tayspen72/BluetoothBlinker/BluetoothBlinker-MCU-rust/src/main.rs

//==============================================================================
// Notes
//==============================================================================
// main.rs

//==============================================================================
// Crates and Mods
//==============================================================================
#![no_std]
#![no_main]

use cortex_m_rt::entry;
use panic_halt as _; // Breakpoint on `rust_begin_unwind` to catch panics

mod config;
mod mcu;

//==============================================================================
// Enums, Structs, and Types
//==============================================================================


//==============================================================================
// Variables
//==============================================================================


//==============================================================================
// Main
//==============================================================================
#[entry]
fn main() -> ! {

	init();
	
	loop {
		task_handler();
	}
}

//==============================================================================
// Private Functions
//==============================================================================
fn init() {
	mcu::init();
}

//==============================================================================
// Task Handler
//==============================================================================
fn task_handler() {
	mcu::task_handler();
}
