tayspen72/BluetoothBlinker/BluetoothBlinker-MCU-c/cc26x0r2/inc/hw_ccfg.h

/******************************************************************************
*  Filename:       hw_ccfg_h
*  Revised:        2017-02-16 09:17:04 +0100 (Thu, 16 Feb 2017)
*  Revision:       48471
*
* Copyright (c) 2015 - 2017, Texas Instruments Incorporated
* All rights reserved.
*
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
* 3) Neither the name of the ORGANIZATION nor the names of its contributors may
*    be used to endorse or promote products derived from this software without
*    specific prior written permission.
*
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
******************************************************************************/

#ifndef __HW_CCFG_H__
#define __HW_CCFG_H__

//*****************************************************************************
//
// This section defines the register offsets of
// CCFG component
//
//*****************************************************************************
// Extern LF clock configuration
#define CCFG_O_EXT_LF_CLK                                           0x00000FA8

// Mode Configuration 1
#define CCFG_O_MODE_CONF_1                                          0x00000FAC

// CCFG Size and Disable Flags
#define CCFG_O_SIZE_AND_DIS_FLAGS                                   0x00000FB0

// Mode Configuration 0
#define CCFG_O_MODE_CONF                                            0x00000FB4

// Voltage Load 0
#define CCFG_O_VOLT_LOAD_0                                          0x00000FB8

// Voltage Load 1
#define CCFG_O_VOLT_LOAD_1                                          0x00000FBC

// Real Time Clock Offset
#define CCFG_O_RTC_OFFSET                                           0x00000FC0

// Frequency Offset
#define CCFG_O_FREQ_OFFSET                                          0x00000FC4

// IEEE MAC Address 0
#define CCFG_O_IEEE_MAC_0                                           0x00000FC8

// IEEE MAC Address 1
#define CCFG_O_IEEE_MAC_1                                           0x00000FCC

// IEEE BLE Address 0
#define CCFG_O_IEEE_BLE_0                                           0x00000FD0

// IEEE BLE Address 1
#define CCFG_O_IEEE_BLE_1                                           0x00000FD4

// Bootloader Configuration
#define CCFG_O_BL_CONFIG                                            0x00000FD8

// Erase Configuration
#define CCFG_O_ERASE_CONF                                           0x00000FDC

// TI Options
#define CCFG_O_CCFG_TI_OPTIONS                                      0x00000FE0

// Test Access Points Enable 0
#define CCFG_O_CCFG_TAP_DAP_0                                       0x00000FE4

// Test Access Points Enable 1
#define CCFG_O_CCFG_TAP_DAP_1                                       0x00000FE8

// Image Valid
#define CCFG_O_IMAGE_VALID_CONF                                     0x00000FEC

// Protect Sectors 0-31
#define CCFG_O_CCFG_PROT_31_0                                       0x00000FF0

// Protect Sectors 32-63
#define CCFG_O_CCFG_PROT_63_32                                      0x00000FF4

// Protect Sectors 64-95
#define CCFG_O_CCFG_PROT_95_64                                      0x00000FF8

// Protect Sectors 96-127
#define CCFG_O_CCFG_PROT_127_96                                     0x00000FFC

//*****************************************************************************
//
// Register: CCFG_O_EXT_LF_CLK
//
//*****************************************************************************
// Field: [31:24] DIO
//
// Unsigned integer, selecting the DIO to supply external 32kHz clock as
// SCLK_LF when MODE_CONF.SCLK_LF_OPTION is set to EXTERNAL. The selected DIO
// will be marked as reserved by the pin driver (TI-RTOS environment) and hence
// not selectable for other usage.
#define CCFG_EXT_LF_CLK_DIO_W                                                8
#define CCFG_EXT_LF_CLK_DIO_M                                       0xFF000000
#define CCFG_EXT_LF_CLK_DIO_S                                               24

// Field:  [23:0] RTC_INCREMENT
//
// Unsigned integer, defining the input frequency of the external clock and is
// written to AON_RTC:SUBSECINC.VALUEINC. Defined as follows:
// EXT_LF_CLK.RTC_INCREMENT = 2^38/InputClockFrequency in Hertz (e.g.:
// RTC_INCREMENT=0x800000 for InputClockFrequency=32768 Hz)
#define CCFG_EXT_LF_CLK_RTC_INCREMENT_W                                     24
#define CCFG_EXT_LF_CLK_RTC_INCREMENT_M                             0x00FFFFFF
#define CCFG_EXT_LF_CLK_RTC_INCREMENT_S                                      0

//*****************************************************************************
//
// Register: CCFG_O_MODE_CONF_1
//
//*****************************************************************************
// Field: [23:20] ALT_DCDC_VMIN
//
// Minimum voltage for when DC/DC should be used if alternate DC/DC setting is
// enabled (SIZE_AND_DIS_FLAGS.DIS_ALT_DCDC_SETTING=0).
// Voltage = (28 + ALT_DCDC_VMIN) / 16.
// 0: 1.75V
// 1: 1.8125V
// ...
// 14: 2.625V
// 15: 2.6875V
//
// NOTE! The DriverLib function SysCtrl_DCDC_VoltageConditionalControl() must
// be called regularly to apply this field (handled automatically if using TI
// RTOS!).
#define CCFG_MODE_CONF_1_ALT_DCDC_VMIN_W                                     4
#define CCFG_MODE_CONF_1_ALT_DCDC_VMIN_M                            0x00F00000
#define CCFG_MODE_CONF_1_ALT_DCDC_VMIN_S                                    20

// Field:    [19] ALT_DCDC_DITHER_EN
//
// Enable DC/DC dithering if alternate DC/DC setting is enabled
// (SIZE_AND_DIS_FLAGS.DIS_ALT_DCDC_SETTING=0).
// 0: Dither disable
// 1: Dither enable
#define CCFG_MODE_CONF_1_ALT_DCDC_DITHER_EN                         0x00080000
#define CCFG_MODE_CONF_1_ALT_DCDC_DITHER_EN_BITN                            19
#define CCFG_MODE_CONF_1_ALT_DCDC_DITHER_EN_M                       0x00080000
#define CCFG_MODE_CONF_1_ALT_DCDC_DITHER_EN_S                               19

// Field: [18:16] ALT_DCDC_IPEAK
//
// Inductor peak current if alternate DC/DC setting is enabled
// (SIZE_AND_DIS_FLAGS.DIS_ALT_DCDC_SETTING=0). Assuming 10uH external
// inductor!
// Peak current = 31 + ( 4 * ALT_DCDC_IPEAK ) :
// 0: 31mA (min)
// ...
// 4: 47mA
// ...
// 7: 59mA (max)
#define CCFG_MODE_CONF_1_ALT_DCDC_IPEAK_W                                    3
#define CCFG_MODE_CONF_1_ALT_DCDC_IPEAK_M                           0x00070000
#define CCFG_MODE_CONF_1_ALT_DCDC_IPEAK_S                                   16

// Field: [15:12] DELTA_IBIAS_INIT
//
// Signed delta value for IBIAS_INIT. Delta value only applies if
// SIZE_AND_DIS_FLAGS.DIS_XOSC_OVR=0.
// See FCFG1:AMPCOMP_CTRL1.IBIAS_INIT
#define CCFG_MODE_CONF_1_DELTA_IBIAS_INIT_W                                  4
#define CCFG_MODE_CONF_1_DELTA_IBIAS_INIT_M                         0x0000F000
#define CCFG_MODE_CONF_1_DELTA_IBIAS_INIT_S                                 12

// Field:  [11:8] DELTA_IBIAS_OFFSET
//
// Signed delta value for IBIAS_OFFSET. Delta value only applies if
// SIZE_AND_DIS_FLAGS.DIS_XOSC_OVR=0.
// See FCFG1:AMPCOMP_CTRL1.IBIAS_OFFSET
#define CCFG_MODE_CONF_1_DELTA_IBIAS_OFFSET_W                                4
#define CCFG_MODE_CONF_1_DELTA_IBIAS_OFFSET_M                       0x00000F00
#define CCFG_MODE_CONF_1_DELTA_IBIAS_OFFSET_S                                8

// Field:   [7:0] XOSC_MAX_START
//
// Unsigned value of maximum XOSC startup time (worst case) in units of 100us.
// Value only applies if SIZE_AND_DIS_FLAGS.DIS_XOSC_OVR=0.
#define CCFG_MODE_CONF_1_XOSC_MAX_START_W                                    8
#define CCFG_MODE_CONF_1_XOSC_MAX_START_M                           0x000000FF
#define CCFG_MODE_CONF_1_XOSC_MAX_START_S                                    0

//*****************************************************************************
//
// Register: CCFG_O_SIZE_AND_DIS_FLAGS
//
//*****************************************************************************
// Field: [31:16] SIZE_OF_CCFG
//
// Total size of CCFG in bytes.
#define CCFG_SIZE_AND_DIS_FLAGS_SIZE_OF_CCFG_W                              16
#define CCFG_SIZE_AND_DIS_FLAGS_SIZE_OF_CCFG_M                      0xFFFF0000
#define CCFG_SIZE_AND_DIS_FLAGS_SIZE_OF_CCFG_S                              16

// Field:  [15:4] DISABLE_FLAGS
//
// Reserved for future use. Software should not rely on the value of a
// reserved. Writing any other value than the reset/default value may result in
// undefined behavior.
#define CCFG_SIZE_AND_DIS_FLAGS_DISABLE_FLAGS_W                             12
#define CCFG_SIZE_AND_DIS_FLAGS_DISABLE_FLAGS_M                     0x0000FFF0
#define CCFG_SIZE_AND_DIS_FLAGS_DISABLE_FLAGS_S                              4

// Field:     [3] DIS_TCXO
//
// Disable TCXO.
// 0: TCXO functionality enabled.
// 1: TCXO functionality disabled.
// Note:
// An external TCXO is required if DIS_TCXO = 0.
#define CCFG_SIZE_AND_DIS_FLAGS_DIS_TCXO                            0x00000008
#define CCFG_SIZE_AND_DIS_FLAGS_DIS_TCXO_BITN                                3
#define CCFG_SIZE_AND_DIS_FLAGS_DIS_TCXO_M                          0x00000008
#define CCFG_SIZE_AND_DIS_FLAGS_DIS_TCXO_S                                   3

// Field:     [2] DIS_GPRAM
//
// Disable GPRAM (or use the 8K VIMS RAM as CACHE RAM).
// 0: GPRAM is enabled and hence CACHE disabled.
// 1: GPRAM is disabled and instead CACHE is enabled (default).
// Notes:
// - Disabling CACHE will reduce CPU execution speed (up to 60%).
// - GPRAM is 8 K-bytes in size and located at 0x11000000-0x11001FFF if
// enabled.
// See:
// VIMS:CTL.MODE
#define CCFG_SIZE_AND_DIS_FLAGS_DIS_GPRAM                           0x00000004
#define CCFG_SIZE_AND_DIS_FLAGS_DIS_GPRAM_BITN                               2
#define CCFG_SIZE_AND_DIS_FLAGS_DIS_GPRAM_M                         0x00000004
#define CCFG_SIZE_AND_DIS_FLAGS_DIS_GPRAM_S                                  2

// Field:     [1] DIS_ALT_DCDC_SETTING
//
// Disable alternate DC/DC settings.
// 0: Enable alternate DC/DC settings.
// 1: Disable alternate DC/DC settings.
// See:
// MODE_CONF_1.ALT_DCDC_VMIN
// MODE_CONF_1.ALT_DCDC_DITHER_EN
// MODE_CONF_1.ALT_DCDC_IPEAK
//
// NOTE! The DriverLib function SysCtrl_DCDC_VoltageConditionalControl() must
// be called regularly to apply this field (handled automatically if using TI
// RTOS!).
#define CCFG_SIZE_AND_DIS_FLAGS_DIS_ALT_DCDC_SETTING                0x00000002
#define CCFG_SIZE_AND_DIS_FLAGS_DIS_ALT_DCDC_SETTING_BITN                    1
#define CCFG_SIZE_AND_DIS_FLAGS_DIS_ALT_DCDC_SETTING_M              0x00000002
#define CCFG_SIZE_AND_DIS_FLAGS_DIS_ALT_DCDC_SETTING_S                       1

// Field:     [0] DIS_XOSC_OVR
//
// Disable XOSC override functionality.
// 0: Enable XOSC override functionality.
// 1: Disable XOSC override functionality.
// See:
// MODE_CONF_1.DELTA_IBIAS_INIT
// MODE_CONF_1.DELTA_IBIAS_OFFSET
// MODE_CONF_1.XOSC_MAX_START
#define CCFG_SIZE_AND_DIS_FLAGS_DIS_XOSC_OVR                        0x00000001
#define CCFG_SIZE_AND_DIS_FLAGS_DIS_XOSC_OVR_BITN                            0
#define CCFG_SIZE_AND_DIS_FLAGS_DIS_XOSC_OVR_M                      0x00000001
#define CCFG_SIZE_AND_DIS_FLAGS_DIS_XOSC_OVR_S                               0

//*****************************************************************************
//
// Register: CCFG_O_MODE_CONF
//
//*****************************************************************************
// Field: [31:28] VDDR_TRIM_SLEEP_DELTA
//
// Signed delta value to apply to the
// VDDR_TRIM_SLEEP target, minus one. See FCFG1:VOLT_TRIM.VDDR_TRIM_SLEEP_H.
// 0x8 (-8) : Delta = -7
// ...
// 0xF (-1) : Delta = 0
// 0x0 (0) : Delta = +1
// ...
// 0x7 (7) : Delta = +8
#define CCFG_MODE_CONF_VDDR_TRIM_SLEEP_DELTA_W                               4
#define CCFG_MODE_CONF_VDDR_TRIM_SLEEP_DELTA_M                      0xF0000000
#define CCFG_MODE_CONF_VDDR_TRIM_SLEEP_DELTA_S                              28

// Field:    [27] DCDC_RECHARGE
//
// DC/DC during recharge in powerdown.
// 0: Use the DC/DC during recharge in powerdown.
// 1: Do not use the DC/DC during recharge in powerdown (default).
//
// NOTE! The DriverLib function SysCtrl_DCDC_VoltageConditionalControl() must
// be called regularly to apply this field (handled automatically if using TI
// RTOS!).
#define CCFG_MODE_CONF_DCDC_RECHARGE                                0x08000000
#define CCFG_MODE_CONF_DCDC_RECHARGE_BITN                                   27
#define CCFG_MODE_CONF_DCDC_RECHARGE_M                              0x08000000
#define CCFG_MODE_CONF_DCDC_RECHARGE_S                                      27

// Field:    [26] DCDC_ACTIVE
//
// DC/DC in active mode.
// 0: Use the DC/DC during active mode.
// 1: Do not use the DC/DC during active mode (default).
//
// NOTE! The DriverLib function SysCtrl_DCDC_VoltageConditionalControl() must
// be called regularly to apply this field (handled automatically if using TI
// RTOS!).
#define CCFG_MODE_CONF_DCDC_ACTIVE                                  0x04000000
#define CCFG_MODE_CONF_DCDC_ACTIVE_BITN                                     26
#define CCFG_MODE_CONF_DCDC_ACTIVE_M                                0x04000000
#define CCFG_MODE_CONF_DCDC_ACTIVE_S                                        26

// Field:    [25] VDDR_EXT_LOAD
//
// Reserved for future use. Software should not rely on the value of a
// reserved. Writing any other value than the reset/default value may result in
// undefined behavior.
#define CCFG_MODE_CONF_VDDR_EXT_LOAD                                0x02000000
#define CCFG_MODE_CONF_VDDR_EXT_LOAD_BITN                                   25
#define CCFG_MODE_CONF_VDDR_EXT_LOAD_M                              0x02000000
#define CCFG_MODE_CONF_VDDR_EXT_LOAD_S                                      25

// Field:    [24] VDDS_BOD_LEVEL
//
// VDDS BOD level.
// 0: VDDS BOD level is 2.0 V (necessary for maximum PA output power on
// CC13x0).
// 1: VDDS BOD level is 1.8 V (or 1.7 V for external regulator mode) (default).
#define CCFG_MODE_CONF_VDDS_BOD_LEVEL                               0x01000000
#define CCFG_MODE_CONF_VDDS_BOD_LEVEL_BITN                                  24
#define CCFG_MODE_CONF_VDDS_BOD_LEVEL_M                             0x01000000
#define CCFG_MODE_CONF_VDDS_BOD_LEVEL_S                                     24

// Field: [23:22] SCLK_LF_OPTION
//
// Select source for SCLK_LF.
// ENUMs:
// RCOSC_LF                 Low frequency RCOSC (default)
// XOSC_LF                  32.768kHz low frequency XOSC
// EXTERNAL_LF              External low frequency clock on DIO defined by
//                          EXT_LF_CLK.DIO. The RTC tick speed
//                          AON_RTC:SUBSECINC is updated to
//                          EXT_LF_CLK.RTC_INCREMENT (done in the
//                          trimDevice() xxWare boot function). External
//                          clock must always be running when the chip is
//                          in standby for VDDR recharge timing.
// XOSC_HF_DLF              31.25kHz clock derived from 24MHz XOSC (dividing
//                          by 768 in HW). The RTC tick speed
//                          [AON_RTC.SUBSECINC.*] is updated to 0x8637BD,
//                          corresponding to a 31.25kHz clock (done in the
//                          trimDevice() xxWare boot function). Standby
//                          power mode is not supported when using this
//                          clock source.
#define CCFG_MODE_CONF_SCLK_LF_OPTION_W                                      2
#define CCFG_MODE_CONF_SCLK_LF_OPTION_M                             0x00C00000
#define CCFG_MODE_CONF_SCLK_LF_OPTION_S                                     22
#define CCFG_MODE_CONF_SCLK_LF_OPTION_RCOSC_LF                      0x00C00000
#define CCFG_MODE_CONF_SCLK_LF_OPTION_XOSC_LF                       0x00800000
#define CCFG_MODE_CONF_SCLK_LF_OPTION_EXTERNAL_LF                   0x00400000
#define CCFG_MODE_CONF_SCLK_LF_OPTION_XOSC_HF_DLF                   0x00000000

// Field:    [21] VDDR_TRIM_SLEEP_TC
//
// 0x1: VDDR_TRIM_SLEEP_DELTA is not temperature compensated
// 0x0: RTOS/driver temperature compensates VDDR_TRIM_SLEEP_DELTA every time
// standby mode is entered. This improves low-temperature RCOSC_LF frequency
// stability in standby mode.
//
// When temperature compensation is performed, the delta is calculates this
// way:
// Delta = max (delta, min(8, floor(62-temp)/8))
// Here, delta is given by VDDR_TRIM_SLEEP_DELTA, and temp is the current
// temperature in degrees C.
#define CCFG_MODE_CONF_VDDR_TRIM_SLEEP_TC                           0x00200000
#define CCFG_MODE_CONF_VDDR_TRIM_SLEEP_TC_BITN                              21
#define CCFG_MODE_CONF_VDDR_TRIM_SLEEP_TC_M                         0x00200000
#define CCFG_MODE_CONF_VDDR_TRIM_SLEEP_TC_S                                 21

// Field:    [20] RTC_COMP
//
// Reserved for future use. Software should not rely on the value of a
// reserved. Writing any other value than the reset/default value may result in
// undefined behavior.
#define CCFG_MODE_CONF_RTC_COMP                                     0x00100000
#define CCFG_MODE_CONF_RTC_COMP_BITN                                        20
#define CCFG_MODE_CONF_RTC_COMP_M                                   0x00100000
#define CCFG_MODE_CONF_RTC_COMP_S                                           20

// Field: [19:18] XOSC_FREQ
//
// Reserved for future use. Software should not rely on the value of a
// reserved. Writing any other value than the reset/default value may result in
// undefined behavior.
// ENUMs:
// 24M                      24 MHz XOSC_HF
// 48M                      48 MHz XOSC_HF
// HPOSC                    HPOSC
#define CCFG_MODE_CONF_XOSC_FREQ_W                                           2
#define CCFG_MODE_CONF_XOSC_FREQ_M                                  0x000C0000
#define CCFG_MODE_CONF_XOSC_FREQ_S                                          18
#define CCFG_MODE_CONF_XOSC_FREQ_24M                                0x000C0000
#define CCFG_MODE_CONF_XOSC_FREQ_48M                                0x00080000
#define CCFG_MODE_CONF_XOSC_FREQ_HPOSC                              0x00040000

// Field:    [17] XOSC_CAP_MOD
//
// Enable modification (delta) to XOSC cap-array. Value specified in
// XOSC_CAPARRAY_DELTA.
// 0: Apply cap-array delta
// 1: Do not apply cap-array delta (default)
#define CCFG_MODE_CONF_XOSC_CAP_MOD                                 0x00020000
#define CCFG_MODE_CONF_XOSC_CAP_MOD_BITN                                    17
#define CCFG_MODE_CONF_XOSC_CAP_MOD_M                               0x00020000
#define CCFG_MODE_CONF_XOSC_CAP_MOD_S                                       17

// Field:    [16] HF_COMP
//
// Reserved for future use. Software should not rely on the value of a
// reserved. Writing any other value than the reset/default value may result in
// undefined behavior.
#define CCFG_MODE_CONF_HF_COMP                                      0x00010000
#define CCFG_MODE_CONF_HF_COMP_BITN                                         16
#define CCFG_MODE_CONF_HF_COMP_M                                    0x00010000
#define CCFG_MODE_CONF_HF_COMP_S                                            16

// Field:  [15:8] XOSC_CAPARRAY_DELTA
//
// Signed 8-bit value, directly modifying trimmed XOSC cap-array step value.
// Enabled by XOSC_CAP_MOD.
#define CCFG_MODE_CONF_XOSC_CAPARRAY_DELTA_W                                 8
#define CCFG_MODE_CONF_XOSC_CAPARRAY_DELTA_M                        0x0000FF00
#define CCFG_MODE_CONF_XOSC_CAPARRAY_DELTA_S                                 8

// Field:   [7:0] VDDR_CAP
//
// Unsigned 8-bit integer, representing the minimum decoupling capacitance
// (worst case) on VDDR, in units of 100nF. This should take into account
// capacitor tolerance and voltage dependent capacitance variation. This bit
// affects the recharge period calculation when going into powerdown or
// standby.
//
// NOTE! If using the following functions this field must be configured (used
// by TI RTOS):
// SysCtrlSetRechargeBeforePowerDown() SysCtrlAdjustRechargeAfterPowerDown()
#define CCFG_MODE_CONF_VDDR_CAP_W                                            8
#define CCFG_MODE_CONF_VDDR_CAP_M                                   0x000000FF
#define CCFG_MODE_CONF_VDDR_CAP_S                                            0

//*****************************************************************************
//
// Register: CCFG_O_VOLT_LOAD_0
//
//*****************************************************************************
// Field: [31:24] VDDR_EXT_TP45
//
// Reserved for future use. Software should not rely on the value of a
// reserved. Writing any other value than the reset/default value may result in
// undefined behavior.
#define CCFG_VOLT_LOAD_0_VDDR_EXT_TP45_W                                     8
#define CCFG_VOLT_LOAD_0_VDDR_EXT_TP45_M                            0xFF000000
#define CCFG_VOLT_LOAD_0_VDDR_EXT_TP45_S                                    24

// Field: [23:16] VDDR_EXT_TP25
//
// Reserved for future use. Software should not rely on the value of a
// reserved. Writing any other value than the reset/default value may result in
// undefined behavior.
#define CCFG_VOLT_LOAD_0_VDDR_EXT_TP25_W                                     8
#define CCFG_VOLT_LOAD_0_VDDR_EXT_TP25_M                            0x00FF0000
#define CCFG_VOLT_LOAD_0_VDDR_EXT_TP25_S                                    16

// Field:  [15:8] VDDR_EXT_TP5
//
// Reserved for future use. Software should not rely on the value of a
// reserved. Writing any other value than the reset/default value may result in
// undefined behavior.
#define CCFG_VOLT_LOAD_0_VDDR_EXT_TP5_W                                      8
#define CCFG_VOLT_LOAD_0_VDDR_EXT_TP5_M                             0x0000FF00
#define CCFG_VOLT_LOAD_0_VDDR_EXT_TP5_S                                      8

// Field:   [7:0] VDDR_EXT_TM15
//
// Reserved for future use. Software should not rely on the value of a
// reserved. Writing any other value than the reset/default value may result in
// undefined behavior.
#define CCFG_VOLT_LOAD_0_VDDR_EXT_TM15_W                                     8
#define CCFG_VOLT_LOAD_0_VDDR_EXT_TM15_M                            0x000000FF
#define CCFG_VOLT_LOAD_0_VDDR_EXT_TM15_S                                     0

//*****************************************************************************
//
// Register: CCFG_O_VOLT_LOAD_1
//
//*****************************************************************************
// Field: [31:24] VDDR_EXT_TP125
//
// Reserved for future use. Software should not rely on the value of a
// reserved. Writing any other value than the reset/default value may result in
// undefined behavior.
#define CCFG_VOLT_LOAD_1_VDDR_EXT_TP125_W                                    8
#define CCFG_VOLT_LOAD_1_VDDR_EXT_TP125_M                           0xFF000000
#define CCFG_VOLT_LOAD_1_VDDR_EXT_TP125_S                                   24

// Field: [23:16] VDDR_EXT_TP105
//
// Reserved for future use. Software should not rely on the value of a
// reserved. Writing any other value than the reset/default value may result in
// undefined behavior.
#define CCFG_VOLT_LOAD_1_VDDR_EXT_TP105_W                                    8
#define CCFG_VOLT_LOAD_1_VDDR_EXT_TP105_M                           0x00FF0000
#define CCFG_VOLT_LOAD_1_VDDR_EXT_TP105_S                                   16

// Field:  [15:8] VDDR_EXT_TP85
//
// Reserved for future use. Software should not rely on the value of a
// reserved. Writing any other value than the reset/default value may result in
// undefined behavior.
#define CCFG_VOLT_LOAD_1_VDDR_EXT_TP85_W                                     8
#define CCFG_VOLT_LOAD_1_VDDR_EXT_TP85_M                            0x0000FF00
#define CCFG_VOLT_LOAD_1_VDDR_EXT_TP85_S                                     8

// Field:   [7:0] VDDR_EXT_TP65
//
// Reserved for future use. Software should not rely on the value of a
// reserved. Writing any other value than the reset/default value may result in
// undefined behavior.
#define CCFG_VOLT_LOAD_1_VDDR_EXT_TP65_W                                     8
#define CCFG_VOLT_LOAD_1_VDDR_EXT_TP65_M                            0x000000FF
#define CCFG_VOLT_LOAD_1_VDDR_EXT_TP65_S                                     0

//*****************************************************************************
//
// Register: CCFG_O_RTC_OFFSET
//
//*****************************************************************************
// Field: [31:16] RTC_COMP_P0
//
// Reserved for future use. Software should not rely on the value of a
// reserved. Writing any other value than the reset/default value may result in
// undefined behavior.
#define CCFG_RTC_OFFSET_RTC_COMP_P0_W                                       16
#define CCFG_RTC_OFFSET_RTC_COMP_P0_M                               0xFFFF0000
#define CCFG_RTC_OFFSET_RTC_COMP_P0_S                                       16

// Field:  [15:8] RTC_COMP_P1
//
// Reserved for future use. Software should not rely on the value of a
// reserved. Writing any other value than the reset/default value may result in
// undefined behavior.
#define CCFG_RTC_OFFSET_RTC_COMP_P1_W                                        8
#define CCFG_RTC_OFFSET_RTC_COMP_P1_M                               0x0000FF00
#define CCFG_RTC_OFFSET_RTC_COMP_P1_S                                        8

// Field:   [7:0] RTC_COMP_P2
//
// Reserved for future use. Software should not rely on the value of a
// reserved. Writing any other value than the reset/default value may result in
// undefined behavior.
#define CCFG_RTC_OFFSET_RTC_COMP_P2_W                                        8
#define CCFG_RTC_OFFSET_RTC_COMP_P2_M                               0x000000FF
#define CCFG_RTC_OFFSET_RTC_COMP_P2_S                                        0

//*****************************************************************************
//
// Register: CCFG_O_FREQ_OFFSET
//
//*****************************************************************************
// Field: [31:16] HF_COMP_P0
//
// Reserved for future use. Software should not rely on the value of a
// reserved. Writing any other value than the reset/default value may result in
// undefined behavior.
#define CCFG_FREQ_OFFSET_HF_COMP_P0_W                                       16
#define CCFG_FREQ_OFFSET_HF_COMP_P0_M                               0xFFFF0000
#define CCFG_FREQ_OFFSET_HF_COMP_P0_S                                       16

// Field:  [15:8] HF_COMP_P1
//
// Reserved for future use. Software should not rely on the value of a
// reserved. Writing any other value than the reset/default value may result in
// undefined behavior.
#define CCFG_FREQ_OFFSET_HF_COMP_P1_W                                        8
#define CCFG_FREQ_OFFSET_HF_COMP_P1_M                               0x0000FF00
#define CCFG_FREQ_OFFSET_HF_COMP_P1_S                                        8

// Field:   [7:0] HF_COMP_P2
//
// Reserved for future use. Software should not rely on the value of a
// reserved. Writing any other value than the reset/default value may result in
// undefined behavior.
#define CCFG_FREQ_OFFSET_HF_COMP_P2_W                                        8
#define CCFG_FREQ_OFFSET_HF_COMP_P2_M                               0x000000FF
#define CCFG_FREQ_OFFSET_HF_COMP_P2_S                                        0

//*****************************************************************************
//
// Register: CCFG_O_IEEE_MAC_0
//
//*****************************************************************************
// Field:  [31:0] ADDR
//
// Bits[31:0] of the 64-bits custom IEEE MAC address.
// If different from 0xFFFFFFFF then the value of this field is applied;
// otherwise use value from FCFG.
#define CCFG_IEEE_MAC_0_ADDR_W                                              32
#define CCFG_IEEE_MAC_0_ADDR_M                                      0xFFFFFFFF
#define CCFG_IEEE_MAC_0_ADDR_S                                               0

//*****************************************************************************
//
// Register: CCFG_O_IEEE_MAC_1
//
//*****************************************************************************
// Field:  [31:0] ADDR
//
// Bits[63:32] of the 64-bits custom IEEE MAC address.
// If different from 0xFFFFFFFF then the value of this field is applied;
// otherwise use value from FCFG.
#define CCFG_IEEE_MAC_1_ADDR_W                                              32
#define CCFG_IEEE_MAC_1_ADDR_M                                      0xFFFFFFFF
#define CCFG_IEEE_MAC_1_ADDR_S                                               0

//*****************************************************************************
//
// Register: CCFG_O_IEEE_BLE_0
//
//*****************************************************************************
// Field:  [31:0] ADDR
//
// Bits[31:0] of the 64-bits custom IEEE BLE address.
// If different from 0xFFFFFFFF then the value of this field is applied;
// otherwise use value from FCFG.
#define CCFG_IEEE_BLE_0_ADDR_W                                              32
#define CCFG_IEEE_BLE_0_ADDR_M                                      0xFFFFFFFF
#define CCFG_IEEE_BLE_0_ADDR_S                                               0

//*****************************************************************************
//
// Register: CCFG_O_IEEE_BLE_1
//
//*****************************************************************************
// Field:  [31:0] ADDR
//
// Bits[63:32] of the 64-bits custom IEEE BLE address.
// If different from 0xFFFFFFFF then the value of this field is applied;
// otherwise use value from FCFG.
#define CCFG_IEEE_BLE_1_ADDR_W                                              32
#define CCFG_IEEE_BLE_1_ADDR_M                                      0xFFFFFFFF
#define CCFG_IEEE_BLE_1_ADDR_S                                               0

//*****************************************************************************
//
// Register: CCFG_O_BL_CONFIG
//
//*****************************************************************************
// Field: [31:24] BOOTLOADER_ENABLE
//
// Bootloader enable. Boot loader can be accessed if
// IMAGE_VALID_CONF.IMAGE_VALID is non-zero or BL_ENABLE is enabled (and
// conditions for boot loader backdoor are met).
// 0xC5: Boot loader is enabled.
// Any other value: Boot loader is disabled.
#define CCFG_BL_CONFIG_BOOTLOADER_ENABLE_W                                   8
#define CCFG_BL_CONFIG_BOOTLOADER_ENABLE_M                          0xFF000000
#define CCFG_BL_CONFIG_BOOTLOADER_ENABLE_S                                  24

// Field:    [16] BL_LEVEL
//
// Sets the active level of the selected DIO number BL_PIN_NUMBER if boot
// loader backdoor is enabled by the BL_ENABLE field.
// 0: Active low.
// 1: Active high.
#define CCFG_BL_CONFIG_BL_LEVEL                                     0x00010000
#define CCFG_BL_CONFIG_BL_LEVEL_BITN                                        16
#define CCFG_BL_CONFIG_BL_LEVEL_M                                   0x00010000
#define CCFG_BL_CONFIG_BL_LEVEL_S                                           16

// Field:  [15:8] BL_PIN_NUMBER
//
// DIO number that is level checked if the boot loader backdoor is enabled by
// the BL_ENABLE field.
#define CCFG_BL_CONFIG_BL_PIN_NUMBER_W                                       8
#define CCFG_BL_CONFIG_BL_PIN_NUMBER_M                              0x0000FF00
#define CCFG_BL_CONFIG_BL_PIN_NUMBER_S                                       8

// Field:   [7:0] BL_ENABLE
//
// Enables the boot loader backdoor.
// 0xC5: Boot loader backdoor is enabled.
// Any other value: Boot loader backdoor is disabled.
//
// NOTE! Boot loader must be enabled (see BOOTLOADER_ENABLE) if boot loader
// backdoor is enabled.
#define CCFG_BL_CONFIG_BL_ENABLE_W                                           8
#define CCFG_BL_CONFIG_BL_ENABLE_M                                  0x000000FF
#define CCFG_BL_CONFIG_BL_ENABLE_S                                           0

//*****************************************************************************
//
// Register: CCFG_O_ERASE_CONF
//
//*****************************************************************************
// Field:     [8] CHIP_ERASE_DIS_N
//
// Chip erase.
// This bit controls if a chip erase requested through the JTAG WUC TAP will be
// ignored in a following boot caused by a reset of the MCU VD.
// A successful chip erase operation will force the content of the flash main
// bank back to the state as it was when delivered by TI.
// 0: Disable. Any chip erase request detected during boot will be ignored.
// 1: Enable. Any chip erase request detected during boot will be performed by
// the boot FW.
#define CCFG_ERASE_CONF_CHIP_ERASE_DIS_N                            0x00000100
#define CCFG_ERASE_CONF_CHIP_ERASE_DIS_N_BITN                                8
#define CCFG_ERASE_CONF_CHIP_ERASE_DIS_N_M                          0x00000100
#define CCFG_ERASE_CONF_CHIP_ERASE_DIS_N_S                                   8

// Field:     [0] BANK_ERASE_DIS_N
//
// Bank erase.
// This bit controls if the ROM serial boot loader will accept a received Bank
// Erase command (COMMAND_BANK_ERASE).
// A successful Bank Erase operation will erase all main bank sectors not
// protected by write protect configuration bits in CCFG.
// 0: Disable the boot loader bank erase function.
// 1: Enable the boot loader bank erase function.
#define CCFG_ERASE_CONF_BANK_ERASE_DIS_N                            0x00000001
#define CCFG_ERASE_CONF_BANK_ERASE_DIS_N_BITN                                0
#define CCFG_ERASE_CONF_BANK_ERASE_DIS_N_M                          0x00000001
#define CCFG_ERASE_CONF_BANK_ERASE_DIS_N_S                                   0

//*****************************************************************************
//
// Register: CCFG_O_CCFG_TI_OPTIONS
//
//*****************************************************************************
// Field:   [7:0] TI_FA_ENABLE
//
// TI Failure Analysis.
// 0xC5: Enable the functionality of unlocking the TI FA (TI Failure Analysis)
// option with the unlock code.
// All other values: Disable the functionality of unlocking the TI FA option
// with the unlock code.
#define CCFG_CCFG_TI_OPTIONS_TI_FA_ENABLE_W                                  8
#define CCFG_CCFG_TI_OPTIONS_TI_FA_ENABLE_M                         0x000000FF
#define CCFG_CCFG_TI_OPTIONS_TI_FA_ENABLE_S                                  0

//*****************************************************************************
//
// Register: CCFG_O_CCFG_TAP_DAP_0
//
//*****************************************************************************
// Field: [23:16] CPU_DAP_ENABLE
//
// Enable CPU DAP.
// 0xC5: Main CPU DAP access is enabled during power-up/system-reset by ROM
// boot FW.
// Any other value: Main CPU DAP access will remain disabled out of
// power-up/system-reset.
#define CCFG_CCFG_TAP_DAP_0_CPU_DAP_ENABLE_W                                 8
#define CCFG_CCFG_TAP_DAP_0_CPU_DAP_ENABLE_M                        0x00FF0000
#define CCFG_CCFG_TAP_DAP_0_CPU_DAP_ENABLE_S                                16

// Field:  [15:8] PRCM_TAP_ENABLE
//
// Enable PRCM TAP.
// 0xC5: PRCM TAP access is enabled during power-up/system-reset by ROM boot FW
// if enabled by corresponding configuration value in FCFG1 defined by TI.
// Any other value: PRCM TAP access will remain disabled out of
// power-up/system-reset.
#define CCFG_CCFG_TAP_DAP_0_PRCM_TAP_ENABLE_W                                8
#define CCFG_CCFG_TAP_DAP_0_PRCM_TAP_ENABLE_M                       0x0000FF00
#define CCFG_CCFG_TAP_DAP_0_PRCM_TAP_ENABLE_S                                8

// Field:   [7:0] TEST_TAP_ENABLE
//
// Enable Test TAP.
// 0xC5: TEST TAP access is enabled during power-up/system-reset by ROM boot FW
// if enabled by corresponding configuration value in FCFG1 defined by TI.
// Any other value: TEST TAP access will remain disabled out of
// power-up/system-reset.
#define CCFG_CCFG_TAP_DAP_0_TEST_TAP_ENABLE_W                                8
#define CCFG_CCFG_TAP_DAP_0_TEST_TAP_ENABLE_M                       0x000000FF
#define CCFG_CCFG_TAP_DAP_0_TEST_TAP_ENABLE_S                                0

//*****************************************************************************
//
// Register: CCFG_O_CCFG_TAP_DAP_1
//
//*****************************************************************************
// Field: [23:16] PBIST2_TAP_ENABLE
//
// Enable PBIST2 TAP.
// 0xC5: PBIST2 TAP access is enabled during power-up/system-reset by ROM boot
// FW if enabled by corresponding configuration value in FCFG1 defined by TI.
// Any other value: PBIST2 TAP access will remain disabled out of
// power-up/system-reset.
#define CCFG_CCFG_TAP_DAP_1_PBIST2_TAP_ENABLE_W                              8
#define CCFG_CCFG_TAP_DAP_1_PBIST2_TAP_ENABLE_M                     0x00FF0000
#define CCFG_CCFG_TAP_DAP_1_PBIST2_TAP_ENABLE_S                             16

// Field:  [15:8] PBIST1_TAP_ENABLE
//
// Enable PBIST1 TAP.
// 0xC5: PBIST1 TAP access is enabled during power-up/system-reset by ROM boot
// FW if enabled by corresponding configuration value in FCFG1 defined by TI.
// Any other value: PBIST1 TAP access will remain disabled out of
// power-up/system-reset.
#define CCFG_CCFG_TAP_DAP_1_PBIST1_TAP_ENABLE_W                              8
#define CCFG_CCFG_TAP_DAP_1_PBIST1_TAP_ENABLE_M                     0x0000FF00
#define CCFG_CCFG_TAP_DAP_1_PBIST1_TAP_ENABLE_S                              8

// Field:   [7:0] WUC_TAP_ENABLE
//
// Enable WUC TAP
// 0xC5: WUC TAP access is enabled during power-up/system-reset by ROM boot FW
// if enabled by corresponding configuration value in FCFG1 defined by TI.
// Any other value: WUC TAP access will remain disabled out of
// power-up/system-reset.
#define CCFG_CCFG_TAP_DAP_1_WUC_TAP_ENABLE_W                                 8
#define CCFG_CCFG_TAP_DAP_1_WUC_TAP_ENABLE_M                        0x000000FF
#define CCFG_CCFG_TAP_DAP_1_WUC_TAP_ENABLE_S                                 0

//*****************************************************************************
//
// Register: CCFG_O_IMAGE_VALID_CONF
//
//*****************************************************************************
// Field:  [31:0] IMAGE_VALID
//
// This field must have a value of 0x00000000 in order for enabling the boot
// sequence to transfer control to a flash image.
// A non-zero value forces the boot sequence to call the boot loader.
//
// For CC2640R2:
// This field must have the address value of the start of the flash vector
// table in order for enabling the boot sequence to transfer control to a flash
// image.
// Any illegal vector table start address value forces the boot sequence to
// call the boot loader.
// Note that if any other legal vector table start address value than 0x0 is
// selected the PRCM:WARMRESET.WR_TO_PINRESET must be set to 1.
#define CCFG_IMAGE_VALID_CONF_IMAGE_VALID_W                                 32
#define CCFG_IMAGE_VALID_CONF_IMAGE_VALID_M                         0xFFFFFFFF
#define CCFG_IMAGE_VALID_CONF_IMAGE_VALID_S                                  0

//*****************************************************************************
//
// Register: CCFG_O_CCFG_PROT_31_0
//
//*****************************************************************************
// Field:    [31] WRT_PROT_SEC_31
//
// 0: Sector protected
#define CCFG_CCFG_PROT_31_0_WRT_PROT_SEC_31                         0x80000000
#define CCFG_CCFG_PROT_31_0_WRT_PROT_SEC_31_BITN                            31
#define CCFG_CCFG_PROT_31_0_WRT_PROT_SEC_31_M                       0x80000000
#define CCFG_CCFG_PROT_31_0_WRT_PROT_SEC_31_S                               31

// Field:    [30] WRT_PROT_SEC_30
//
// 0: Sector protected
#define CCFG_CCFG_PROT_31_0_WRT_PROT_SEC_30                         0x40000000
#define CCFG_CCFG_PROT_31_0_WRT_PROT_SEC_30_BITN                            30
#define CCFG_CCFG_PROT_31_0_WRT_PROT_SEC_30_M                       0x40000000
#define CCFG_CCFG_PROT_31_0_WRT_PROT_SEC_30_S                               30

// Field:    [29] WRT_PROT_SEC_29
//
// 0: Sector protected
#define CCFG_CCFG_PROT_31_0_WRT_PROT_SEC_29                         0x20000000
#define CCFG_CCFG_PROT_31_0_WRT_PROT_SEC_29_BITN                            29
#define CCFG_CCFG_PROT_31_0_WRT_PROT_SEC_29_M                       0x20000000
#define CCFG_CCFG_PROT_31_0_WRT_PROT_SEC_29_S                               29

// Field:    [28] WRT_PROT_SEC_28
//
// 0: Sector protected
#define CCFG_CCFG_PROT_31_0_WRT_PROT_SEC_28                         0x10000000
#define CCFG_CCFG_PROT_31_0_WRT_PROT_SEC_28_BITN                            28
#define CCFG_CCFG_PROT_31_0_WRT_PROT_SEC_28_M                       0x10000000
#define CCFG_CCFG_PROT_31_0_WRT_PROT_SEC_28_S                               28

// Field:    [27] WRT_PROT_SEC_27
//
// 0: Sector protected
#define CCFG_CCFG_PROT_31_0_WRT_PROT_SEC_27                         0x08000000
#define CCFG_CCFG_PROT_31_0_WRT_PROT_SEC_27_BITN                            27
#define CCFG_CCFG_PROT_31_0_WRT_PROT_SEC_27_M                       0x08000000
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
#define CCFG_CCFG_PROT_127_96_WRT_PROT_SEC_97_BITN                           1
#define CCFG_CCFG_PROT_127_96_WRT_PROT_SEC_97_M                     0x00000002
#define CCFG_CCFG_PROT_127_96_WRT_PROT_SEC_97_S                              1

// Field:     [0] WRT_PROT_SEC_96
//
// 0: Sector protected
#define CCFG_CCFG_PROT_127_96_WRT_PROT_SEC_96                       0x00000001
#define CCFG_CCFG_PROT_127_96_WRT_PROT_SEC_96_BITN                           0
#define CCFG_CCFG_PROT_127_96_WRT_PROT_SEC_96_M                     0x00000001
#define CCFG_CCFG_PROT_127_96_WRT_PROT_SEC_96_S                              0


#endif // __CCFG__
