tayspen72/BluetoothBlinker/BluetoothBlinker-MCU-c/cc26x0r2/driverlib/rf_ble_cmd.h

/******************************************************************************
*  Filename:       rf_ble_cmd.h
*  Revised:        2017-11-10 10:42:47 +0100 (Fri, 10 Nov 2017)
*  Revision:       18052
*
*  Description:    CC2640R2F API for Bluetooth Low Energy commands
*
*  Copyright (c) 2015 - 2017, Texas Instruments Incorporated
*  All rights reserved.
*
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
*  3) Neither the name of the ORGANIZATION nor the names of its contributors may
*     be used to endorse or promote products derived from this software without
*     specific prior written permission.
*
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
******************************************************************************/

#ifndef __BLE_CMD_H
#define __BLE_CMD_H

#ifndef __RFC_STRUCT
#define __RFC_STRUCT
#endif

#ifndef __RFC_STRUCT_ATTR
#if defined(__GNUC__)
#define __RFC_STRUCT_ATTR __attribute__ ((aligned (4)))
#elif defined(__TI_ARM__)
#define __RFC_STRUCT_ATTR __attribute__ ((__packed__,aligned (4)))
#else
#define __RFC_STRUCT_ATTR
#endif
#endif

//! \addtogroup rfc
//! @{

//! \addtogroup ble_cmd
//! @{

#include <stdint.h>
#include "rf_mailbox.h"
#include "rf_common_cmd.h"

typedef struct __RFC_STRUCT rfc_bleRadioOp_s rfc_bleRadioOp_t;
typedef struct __RFC_STRUCT rfc_ble5RadioOp_s rfc_ble5RadioOp_t;
typedef struct __RFC_STRUCT rfc_CMD_BLE_SLAVE_s rfc_CMD_BLE_SLAVE_t;
typedef struct __RFC_STRUCT rfc_CMD_BLE_MASTER_s rfc_CMD_BLE_MASTER_t;
typedef struct __RFC_STRUCT rfc_CMD_BLE_ADV_s rfc_CMD_BLE_ADV_t;
typedef struct __RFC_STRUCT rfc_CMD_BLE_ADV_DIR_s rfc_CMD_BLE_ADV_DIR_t;
typedef struct __RFC_STRUCT rfc_CMD_BLE_ADV_NC_s rfc_CMD_BLE_ADV_NC_t;
typedef struct __RFC_STRUCT rfc_CMD_BLE_ADV_SCAN_s rfc_CMD_BLE_ADV_SCAN_t;
typedef struct __RFC_STRUCT rfc_CMD_BLE_SCANNER_s rfc_CMD_BLE_SCANNER_t;
typedef struct __RFC_STRUCT rfc_CMD_BLE_INITIATOR_s rfc_CMD_BLE_INITIATOR_t;
typedef struct __RFC_STRUCT rfc_CMD_BLE_GENERIC_RX_s rfc_CMD_BLE_GENERIC_RX_t;
typedef struct __RFC_STRUCT rfc_CMD_BLE_TX_TEST_s rfc_CMD_BLE_TX_TEST_t;
typedef struct __RFC_STRUCT rfc_CMD_BLE_ADV_PAYLOAD_s rfc_CMD_BLE_ADV_PAYLOAD_t;
typedef struct __RFC_STRUCT rfc_CMD_BLE5_RADIO_SETUP_s rfc_CMD_BLE5_RADIO_SETUP_t;
typedef struct __RFC_STRUCT rfc_CMD_BLE5_SLAVE_s rfc_CMD_BLE5_SLAVE_t;
typedef struct __RFC_STRUCT rfc_CMD_BLE5_MASTER_s rfc_CMD_BLE5_MASTER_t;
typedef struct __RFC_STRUCT rfc_CMD_BLE5_ADV_EXT_s rfc_CMD_BLE5_ADV_EXT_t;
typedef struct __RFC_STRUCT rfc_CMD_BLE5_ADV_AUX_s rfc_CMD_BLE5_ADV_AUX_t;
typedef struct __RFC_STRUCT rfc_CMD_BLE5_SCANNER_s rfc_CMD_BLE5_SCANNER_t;
typedef struct __RFC_STRUCT rfc_CMD_BLE5_INITIATOR_s rfc_CMD_BLE5_INITIATOR_t;
typedef struct __RFC_STRUCT rfc_CMD_BLE5_GENERIC_RX_s rfc_CMD_BLE5_GENERIC_RX_t;
typedef struct __RFC_STRUCT rfc_CMD_BLE5_TX_TEST_s rfc_CMD_BLE5_TX_TEST_t;
typedef struct __RFC_STRUCT rfc_CMD_BLE5_ADV_s rfc_CMD_BLE5_ADV_t;
typedef struct __RFC_STRUCT rfc_CMD_BLE5_ADV_DIR_s rfc_CMD_BLE5_ADV_DIR_t;
typedef struct __RFC_STRUCT rfc_CMD_BLE5_ADV_NC_s rfc_CMD_BLE5_ADV_NC_t;
typedef struct __RFC_STRUCT rfc_CMD_BLE5_ADV_SCAN_s rfc_CMD_BLE5_ADV_SCAN_t;
typedef struct __RFC_STRUCT rfc_bleMasterSlavePar_s rfc_bleMasterSlavePar_t;
typedef struct __RFC_STRUCT rfc_bleSlavePar_s rfc_bleSlavePar_t;
typedef struct __RFC_STRUCT rfc_bleMasterPar_s rfc_bleMasterPar_t;
typedef struct __RFC_STRUCT rfc_bleAdvPar_s rfc_bleAdvPar_t;
typedef struct __RFC_STRUCT rfc_bleScannerPar_s rfc_bleScannerPar_t;
typedef struct __RFC_STRUCT rfc_bleInitiatorPar_s rfc_bleInitiatorPar_t;
typedef struct __RFC_STRUCT rfc_bleGenericRxPar_s rfc_bleGenericRxPar_t;
typedef struct __RFC_STRUCT rfc_bleTxTestPar_s rfc_bleTxTestPar_t;
typedef struct __RFC_STRUCT rfc_ble5SlavePar_s rfc_ble5SlavePar_t;
typedef struct __RFC_STRUCT rfc_ble5MasterPar_s rfc_ble5MasterPar_t;
typedef struct __RFC_STRUCT rfc_ble5AdvExtPar_s rfc_ble5AdvExtPar_t;
typedef struct __RFC_STRUCT rfc_ble5AdvAuxPar_s rfc_ble5AdvAuxPar_t;
typedef struct __RFC_STRUCT rfc_ble5AuxChRes_s rfc_ble5AuxChRes_t;
typedef struct __RFC_STRUCT rfc_ble5ScannerPar_s rfc_ble5ScannerPar_t;
typedef struct __RFC_STRUCT rfc_ble5InitiatorPar_s rfc_ble5InitiatorPar_t;
typedef struct __RFC_STRUCT rfc_bleMasterSlaveOutput_s rfc_bleMasterSlaveOutput_t;
typedef struct __RFC_STRUCT rfc_bleAdvOutput_s rfc_bleAdvOutput_t;
typedef struct __RFC_STRUCT rfc_bleScannerOutput_s rfc_bleScannerOutput_t;
typedef struct __RFC_STRUCT rfc_bleInitiatorOutput_s rfc_bleInitiatorOutput_t;
typedef struct __RFC_STRUCT rfc_ble5ScanInitOutput_s rfc_ble5ScanInitOutput_t;
typedef struct __RFC_STRUCT rfc_bleGenericRxOutput_s rfc_bleGenericRxOutput_t;
typedef struct __RFC_STRUCT rfc_bleTxTestOutput_s rfc_bleTxTestOutput_t;
typedef struct __RFC_STRUCT rfc_ble5ExtAdvEntry_s rfc_ble5ExtAdvEntry_t;
typedef struct __RFC_STRUCT rfc_bleWhiteListEntry_s rfc_bleWhiteListEntry_t;
typedef struct __RFC_STRUCT rfc_ble5AdiEntry_s rfc_ble5AdiEntry_t;
typedef struct __RFC_STRUCT rfc_bleRxStatus_s rfc_bleRxStatus_t;
typedef struct __RFC_STRUCT rfc_ble5RxStatus_s rfc_ble5RxStatus_t;

//! \addtogroup bleRadioOp
//! @{
struct __RFC_STRUCT rfc_bleRadioOp_s {
   uint16_t commandNo;                  //!<        The command ID number
   uint16_t status;                     //!< \brief An integer telling the status of the command. This value is
                                        //!<        updated by the radio CPU during operation and may be read by the
                                        //!<        system CPU at any time.
   rfc_radioOp_t *pNextOp;              //!<        Pointer to the next operation to run after this operation is done
   ratmr_t startTime;                   //!<        Absolute or relative start time (depending on the value of <code>startTrigger</code>)
   struct {
      uint8_t triggerType:4;            //!<        The type of trigger
      uint8_t bEnaCmd:1;                //!< \brief 0: No alternative trigger command<br>
                                        //!<        1: CMD_TRIGGER can be used as an alternative trigger
      uint8_t triggerNo:2;              //!<        The trigger number of the CMD_TRIGGER command that triggers this action
      uint8_t pastTrig:1;               //!< \brief 0: A trigger in the past is never triggered, or for start of commands, give an error<br>
                                        //!<        1: A trigger in the past is triggered as soon as possible
   } startTrigger;                      //!<        Identification of the trigger that starts the operation
   struct {
      uint8_t rule:4;                   //!<        Condition for running next command: Rule for how to proceed
      uint8_t nSkip:4;                  //!<        Number of skips + 1 if the rule involves skipping. 0: same, 1: next, 2: skip next, ...
   } condition;
   uint8_t channel;                     //!< \brief Channel to use<br>
                                        //!<        0--39: BLE advertising/data channel index<br>
                                        //!<        60--207: Custom frequency; (2300 + <code>channel</code>) MHz<br>
                                        //!<        255: Use existing frequency<br>
                                        //!<        Others: <i>Reserved</i>
   struct {
      uint8_t init:7;                   //!< \brief If <code>bOverride</code> = 1 or custom frequency is used:<br>
                                        //!<        0: Do not use whitening<br>
                                        //!<        Other value: Initialization for 7-bit LFSR whitener
      uint8_t bOverride:1;              //!< \brief 0: Use default whitening for BLE advertising/data channels<br>
                                        //!<        1: Override whitening initialization with value of init
   } whitening;
   uint8_t* pParams;                    //!<        Pointer to command specific parameter structure
   uint8_t* pOutput;                    //!<        Pointer to command specific output structure
} __RFC_STRUCT_ATTR;

//! @}

//! \addtogroup ble5RadioOp
//! @{
struct __RFC_STRUCT rfc_ble5RadioOp_s {
   uint16_t commandNo;                  //!<        The command ID number
   uint16_t status;                     //!< \brief An integer telling the status of the command. This value is
                                        //!<        updated by the radio CPU during operation and may be read by the
                                        //!<        system CPU at any time.
   rfc_radioOp_t *pNextOp;              //!<        Pointer to the next operation to run after this operation is done
   ratmr_t startTime;                   //!<        Absolute or relative start time (depending on the value of <code>startTrigger</code>)
   struct {
      uint8_t triggerType:4;            //!<        The type of trigger
      uint8_t bEnaCmd:1;                //!< \brief 0: No alternative trigger command<br>
                                        //!<        1: CMD_TRIGGER can be used as an alternative trigger
      uint8_t triggerNo:2;              //!<        The trigger number of the CMD_TRIGGER command that triggers this action
      uint8_t pastTrig:1;               //!< \brief 0: A trigger in the past is never triggered, or for start of commands, give an error<br>
                                        //!<        1: A trigger in the past is triggered as soon as possible
   } startTrigger;                      //!<        Identification of the trigger that starts the operation
   struct {
      uint8_t rule:4;                   //!<        Condition for running next command: Rule for how to proceed
      uint8_t nSkip:4;                  //!<        Number of skips + 1 if the rule involves skipping. 0: same, 1: next, 2: skip next, ...
   } condition;
   uint8_t channel;                     //!< \brief Channel to use<br>
                                        //!<        0--39: BLE advertising/data channel index<br>
                                        //!<        60--207: Custom frequency; (2300 + <code>channel</code>) MHz<br>
                                        //!<        255: Use existing frequency<br>
                                        //!<        Others: <i>Reserved</i>
   struct {
      uint8_t init:7;                   //!< \brief If <code>bOverride</code> = 1 or custom frequency is used:<br>
                                        //!<        0: Do not use whitening<br>
                                        //!<        Other value: Initialization for 7-bit LFSR whitener
      uint8_t bOverride:1;              //!< \brief 0: Use default whitening for BLE advertising/data channels<br>
                                        //!<        1: Override whitening initialization with value of init
   } whitening;
   struct {
      uint8_t mainMode:2;               //!< \brief PHY to use:<br>
                                        //!<        0: 1 Mbps<br>
                                        //!<        1: 2 Mbps<br>
                                        //!<        2: Coded<br>
                                        //!<        3: <i>Reserved</i>
      uint8_t coding:6;                 //!< \brief Coding to use for TX if coded PHY is selected.
                                        //!<        See the Technical Reference Manual for details.
   } phyMode;
   uint8_t rangeDelay;                  //!<        Number of RAT ticks to add to the listening time after T_IFS
   uint16_t txPower;                    //!< \brief Transmit power to use (overrides the one given in radio setup).
                                        //!<        0x0000: Use default TX power.
   uint8_t* pParams;                    //!<        Pointer to command specific parameter structure
   uint8_t* pOutput;                    //!<        Pointer to command specific output structure
} __RFC_STRUCT_ATTR;

//! @}

//! \addtogroup CMD_BLE_SLAVE
//! @{
#define CMD_BLE_SLAVE                                           0x1801
//! BLE Slave Command
struct __RFC_STRUCT rfc_CMD_BLE_SLAVE_s {
   uint16_t commandNo;                  //!<        The command ID number 0x1801
   uint16_t status;                     //!< \brief An integer telling the status of the command. This value is
                                        //!<        updated by the radio CPU during operation and may be read by the
                                        //!<        system CPU at any time.
   rfc_radioOp_t *pNextOp;              //!<        Pointer to the next operation to run after this operation is done
   ratmr_t startTime;                   //!<        Absolute or relative start time (depending on the value of <code>startTrigger</code>)
   struct {
      uint8_t triggerType:4;            //!<        The type of trigger
      uint8_t bEnaCmd:1;                //!< \brief 0: No alternative trigger command<br>
                                        //!<        1: CMD_TRIGGER can be used as an alternative trigger
      uint8_t triggerNo:2;              //!<        The trigger number of the CMD_TRIGGER command that triggers this action
      uint8_t pastTrig:1;               //!< \brief 0: A trigger in the past is never triggered, or for start of commands, give an error<br>
                                        //!<        1: A trigger in the past is triggered as soon as possible
   } startTrigger;                      //!<        Identification of the trigger that starts the operation
   struct {
      uint8_t rule:4;                   //!<        Condition for running next command: Rule for how to proceed
      uint8_t nSkip:4;                  //!<        Number of skips + 1 if the rule involves skipping. 0: same, 1: next, 2: skip next, ...
   } condition;
   uint8_t channel;                     //!< \brief Channel to use<br>
                                        //!<        0--39: BLE advertising/data channel index<br>
                                        //!<        60--207: Custom frequency; (2300 + <code>channel</code>) MHz<br>
                                        //!<        255: Use existing frequency<br>
                                        //!<        Others: <i>Reserved</i>
   struct {
      uint8_t init:7;                   //!< \brief If <code>bOverride</code> = 1 or custom frequency is used:<br>
                                        //!<        0: Do not use whitening<br>
                                        //!<        Other value: Initialization for 7-bit LFSR whitener
      uint8_t bOverride:1;              //!< \brief 0: Use default whitening for BLE advertising/data channels<br>
                                        //!<        1: Override whitening initialization with value of init
   } whitening;
   rfc_bleSlavePar_t *pParams;          //!<        Pointer to command specific parameter structure
   rfc_bleMasterSlaveOutput_t *pOutput; //!<        Pointer to command specific output structure
} __RFC_STRUCT_ATTR;

//! @}

//! \addtogroup CMD_BLE_MASTER
//! @{
#define CMD_BLE_MASTER                                          0x1802
//! BLE Master Command
struct __RFC_STRUCT rfc_CMD_BLE_MASTER_s {
   uint16_t commandNo;                  //!<        The command ID number 0x1802
   uint16_t status;                     //!< \brief An integer telling the status of the command. This value is
                                        //!<        updated by the radio CPU during operation and may be read by the
                                        //!<        system CPU at any time.
   rfc_radioOp_t *pNextOp;              //!<        Pointer to the next operation to run after this operation is done
   ratmr_t startTime;                   //!<        Absolute or relative start time (depending on the value of <code>startTrigger</code>)
   struct {
      uint8_t triggerType:4;            //!<        The type of trigger
      uint8_t bEnaCmd:1;                //!< \brief 0: No alternative trigger command<br>
                                        //!<        1: CMD_TRIGGER can be used as an alternative trigger
      uint8_t triggerNo:2;              //!<        The trigger number of the CMD_TRIGGER command that triggers this action
      uint8_t pastTrig:1;               //!< \brief 0: A trigger in the past is never triggered, or for start of commands, give an error<br>
                                        //!<        1: A trigger in the past is triggered as soon as possible
   } startTrigger;                      //!<        Identification of the trigger that starts the operation
   struct {
      uint8_t rule:4;                   //!<        Condition for running next command: Rule for how to proceed
      uint8_t nSkip:4;                  //!<        Number of skips + 1 if the rule involves skipping. 0: same, 1: next, 2: skip next, ...
   } condition;
   uint8_t channel;                     //!< \brief Channel to use<br>
                                        //!<        0--39: BLE advertising/data channel index<br>
                                        //!<        60--207: Custom frequency; (2300 + <code>channel</code>) MHz<br>
                                        //!<        255: Use existing frequency<br>
                                        //!<        Others: <i>Reserved</i>
   struct {
      uint8_t init:7;                   //!< \brief If <code>bOverride</code> = 1 or custom frequency is used:<br>
                                        //!<        0: Do not use whitening<br>
                                        //!<        Other value: Initialization for 7-bit LFSR whitener
      uint8_t bOverride:1;              //!< \brief 0: Use default whitening for BLE advertising/data channels<br>
                                        //!<        1: Override whitening initialization with value of init
   } whitening;
   rfc_bleMasterPar_t *pParams;         //!<        Pointer to command specific parameter structure
   rfc_bleMasterSlaveOutput_t *pOutput; //!<        Pointer to command specific output structure
} __RFC_STRUCT_ATTR;

//! @}

//! \addtogroup CMD_BLE_ADV
//! @{
#define CMD_BLE_ADV                                             0x1803
//! BLE Connectable Undirected Advertiser Command
struct __RFC_STRUCT rfc_CMD_BLE_ADV_s {
   uint16_t commandNo;                  //!<        The command ID number 0x1803
   uint16_t status;                     //!< \brief An integer telling the status of the command. This value is
                                        //!<        updated by the radio CPU during operation and may be read by the
                                        //!<        system CPU at any time.
   rfc_radioOp_t *pNextOp;              //!<        Pointer to the next operation to run after this operation is done
   ratmr_t startTime;                   //!<        Absolute or relative start time (depending on the value of <code>startTrigger</code>)
   struct {
      uint8_t triggerType:4;            //!<        The type of trigger
      uint8_t bEnaCmd:1;                //!< \brief 0: No alternative trigger command<br>
                                        //!<        1: CMD_TRIGGER can be used as an alternative trigger
      uint8_t triggerNo:2;              //!<        The trigger number of the CMD_TRIGGER command that triggers this action
      uint8_t pastTrig:1;               //!< \brief 0: A trigger in the past is never triggered, or for start of commands, give an error<br>
                                        //!<        1: A trigger in the past is triggered as soon as possible
   } startTrigger;                      //!<        Identification of the trigger that starts the operation
   struct {
      uint8_t rule:4;                   //!<        Condition for running next command: Rule for how to proceed
      uint8_t nSkip:4;                  //!<        Number of skips + 1 if the rule involves skipping. 0: same, 1: next, 2: skip next, ...
   } condition;
   uint8_t channel;                     //!< \brief Channel to use<br>
                                        //!<        0--39: BLE advertising/data channel index<br>
                                        //!<        60--207: Custom frequency; (2300 + <code>channel</code>) MHz<br>
                                        //!<        255: Use existing frequency<br>
                                        //!<        Others: <i>Reserved</i>
   struct {
      uint8_t init:7;                   //!< \brief If <code>bOverride</code> = 1 or custom frequency is used:<br>
                                        //!<        0: Do not use whitening<br>
                                        //!<        Other value: Initialization for 7-bit LFSR whitener
      uint8_t bOverride:1;              //!< \brief 0: Use default whitening for BLE advertising/data channels<br>
                                        //!<        1: Override whitening initialization with value of init
   } whitening;
   rfc_bleAdvPar_t *pParams;            //!<        Pointer to command specific parameter structure
   rfc_bleAdvOutput_t *pOutput;         //!<        Pointer to command specific output structure
} __RFC_STRUCT_ATTR;

//! @}

//! \addtogroup CMD_BLE_ADV_DIR
//! @{
#define CMD_BLE_ADV_DIR                                         0x1804
//! BLE Connectable Directed Advertiser Command
struct __RFC_STRUCT rfc_CMD_BLE_ADV_DIR_s {
   uint16_t commandNo;                  //!<        The command ID number 0x1804
   uint16_t status;                     //!< \brief An integer telling the status of the command. This value is
                                        //!<        updated by the radio CPU during operation and may be read by the
                                        //!<        system CPU at any time.
   rfc_radioOp_t *pNextOp;              //!<        Pointer to the next operation to run after this operation is done
   ratmr_t startTime;                   //!<        Absolute or relative start time (depending on the value of <code>startTrigger</code>)
   struct {
      uint8_t triggerType:4;            //!<        The type of trigger
      uint8_t bEnaCmd:1;                //!< \brief 0: No alternative trigger command<br>
                                        //!<        1: CMD_TRIGGER can be used as an alternative trigger
      uint8_t triggerNo:2;              //!<        The trigger number of the CMD_TRIGGER command that triggers this action
      uint8_t pastTrig:1;               //!< \brief 0: A trigger in the past is never triggered, or for start of commands, give an error<br>
                                        //!<        1: A trigger in the past is triggered as soon as possible
   } startTrigger;                      //!<        Identification of the trigger that starts the operation
   struct {
      uint8_t rule:4;                   //!<        Condition for running next command: Rule for how to proceed
      uint8_t nSkip:4;                  //!<        Number of skips + 1 if the rule involves skipping. 0: same, 1: next, 2: skip next, ...
   } condition;
   uint8_t channel;                     //!< \brief Channel to use<br>
                                        //!<        0--39: BLE advertising/data channel index<br>
                                        //!<        60--207: Custom frequency; (2300 + <code>channel</code>) MHz<br>
                                        //!<        255: Use existing frequency<br>
                                        //!<        Others: <i>Reserved</i>
   struct {
      uint8_t init:7;                   //!< \brief If <code>bOverride</code> = 1 or custom frequency is used:<br>
                                        //!<        0: Do not use whitening<br>
                                        //!<        Other value: Initialization for 7-bit LFSR whitener
      uint8_t bOverride:1;              //!< \brief 0: Use default whitening for BLE advertising/data channels<br>
                                        //!<        1: Override whitening initialization with value of init
   } whitening;
   rfc_bleAdvPar_t *pParams;            //!<        Pointer to command specific parameter structure
   rfc_bleAdvOutput_t *pOutput;         //!<        Pointer to command specific output structure
} __RFC_STRUCT_ATTR;

//! @}

//! \addtogroup CMD_BLE_ADV_NC
//! @{
#define CMD_BLE_ADV_NC                                          0x1805
//! BLE Non-Connectable Advertiser Command
struct __RFC_STRUCT rfc_CMD_BLE_ADV_NC_s {
   uint16_t commandNo;                  //!<        The command ID number 0x1805
   uint16_t status;                     //!< \brief An integer telling the status of the command. This value is
                                        //!<        updated by the radio CPU during operation and may be read by the
                                        //!<        system CPU at any time.
   rfc_radioOp_t *pNextOp;              //!<        Pointer to the next operation to run after this operation is done
   ratmr_t startTime;                   //!<        Absolute or relative start time (depending on the value of <code>startTrigger</code>)
   struct {
      uint8_t triggerType:4;            //!<        The type of trigger
      uint8_t bEnaCmd:1;                //!< \brief 0: No alternative trigger command<br>
                                        //!<        1: CMD_TRIGGER can be used as an alternative trigger
      uint8_t triggerNo:2;              //!<        The trigger number of the CMD_TRIGGER command that triggers this action
      uint8_t pastTrig:1;               //!< \brief 0: A trigger in the past is never triggered, or for start of commands, give an error<br>
                                        //!<        1: A trigger in the past is triggered as soon as possible
   } startTrigger;                      //!<        Identification of the trigger that starts the operation
   struct {
      uint8_t rule:4;                   //!<        Condition for running next command: Rule for how to proceed
      uint8_t nSkip:4;                  //!<        Number of skips + 1 if the rule involves skipping. 0: same, 1: next, 2: skip next, ...
   } condition;
   uint8_t channel;                     //!< \brief Channel to use<br>
                                        //!<        0--39: BLE advertising/data channel index<br>
                                        //!<        60--207: Custom frequency; (2300 + <code>channel</code>) MHz<br>
                                        //!<        255: Use existing frequency<br>
                                        //!<        Others: <i>Reserved</i>
   struct {
      uint8_t init:7;                   //!< \brief If <code>bOverride</code> = 1 or custom frequency is used:<br>
                                        //!<        0: Do not use whitening<br>
                                        //!<        Other value: Initialization for 7-bit LFSR whitener
      uint8_t bOverride:1;              //!< \brief 0: Use default whitening for BLE advertising/data channels<br>
                                        //!<        1: Override whitening initialization with value of init
   } whitening;
   rfc_bleAdvPar_t *pParams;            //!<        Pointer to command specific parameter structure
   rfc_bleAdvOutput_t *pOutput;         //!<        Pointer to command specific output structure
} __RFC_STRUCT_ATTR;

//! @}

//! \addtogroup CMD_BLE_ADV_SCAN
//! @{
#define CMD_BLE_ADV_SCAN                                        0x1806
//! BLE Scannable Undirected Advertiser Command
struct __RFC_STRUCT rfc_CMD_BLE_ADV_SCAN_s {
   uint16_t commandNo;                  //!<        The command ID number 0x1806
   uint16_t status;                     //!< \brief An integer telling the status of the command. This value is
                                        //!<        updated by the radio CPU during operation and may be read by the
                                        //!<        system CPU at any time.
   rfc_radioOp_t *pNextOp;              //!<        Pointer to the next operation to run after this operation is done
   ratmr_t startTime;                   //!<        Absolute or relative start time (depending on the value of <code>startTrigger</code>)
   struct {
      uint8_t triggerType:4;            //!<        The type of trigger
      uint8_t bEnaCmd:1;                //!< \brief 0: No alternative trigger command<br>
                                        //!<        1: CMD_TRIGGER can be used as an alternative trigger
      uint8_t triggerNo:2;              //!<        The trigger number of the CMD_TRIGGER command that triggers this action
      uint8_t pastTrig:1;               //!< \brief 0: A trigger in the past is never triggered, or for start of commands, give an error<br>
                                        //!<        1: A trigger in the past is triggered as soon as possible
   } startTrigger;                      //!<        Identification of the trigger that starts the operation
   struct {
      uint8_t rule:4;                   //!<        Condition for running next command: Rule for how to proceed
      uint8_t nSkip:4;                  //!<        Number of skips + 1 if the rule involves skipping. 0: same, 1: next, 2: skip next, ...
   } condition;
   uint8_t channel;                     //!< \brief Channel to use<br>
                                        //!<        0--39: BLE advertising/data channel index<br>
                                        //!<        60--207: Custom frequency; (2300 + <code>channel</code>) MHz<br>
                                        //!<        255: Use existing frequency<br>
                                        //!<        Others: <i>Reserved</i>
   struct {
      uint8_t init:7;                   //!< \brief If <code>bOverride</code> = 1 or custom frequency is used:<br>
                                        //!<        0: Do not use whitening<br>
                                        //!<        Other value: Initialization for 7-bit LFSR whitener
      uint8_t bOverride:1;              //!< \brief 0: Use default whitening for BLE advertising/data channels<br>
                                        //!<        1: Override whitening initialization with value of init
   } whitening;
   rfc_bleAdvPar_t *pParams;            //!<        Pointer to command specific parameter structure
   rfc_bleAdvOutput_t *pOutput;         //!<        Pointer to command specific output structure
} __RFC_STRUCT_ATTR;

//! @}

//! \addtogroup CMD_BLE_SCANNER
//! @{
#define CMD_BLE_SCANNER                                         0x1807
//! BLE Scanner Command
struct __RFC_STRUCT rfc_CMD_BLE_SCANNER_s {
   uint16_t commandNo;                  //!<        The command ID number 0x1807
   uint16_t status;                     //!< \brief An integer telling the status of the command. This value is
                                        //!<        updated by the radio CPU during operation and may be read by the
                                        //!<        system CPU at any time.
   rfc_radioOp_t *pNextOp;              //!<        Pointer to the next operation to run after this operation is done
   ratmr_t startTime;                   //!<        Absolute or relative start time (depending on the value of <code>startTrigger</code>)
   struct {
      uint8_t triggerType:4;            //!<        The type of trigger
      uint8_t bEnaCmd:1;                //!< \brief 0: No alternative trigger command<br>
                                        //!<        1: CMD_TRIGGER can be used as an alternative trigger
      uint8_t triggerNo:2;              //!<        The trigger number of the CMD_TRIGGER command that triggers this action
      uint8_t pastTrig:1;               //!< \brief 0: A trigger in the past is never triggered, or for start of commands, give an error<br>
                                        //!<        1: A trigger in the past is triggered as soon as possible
   } startTrigger;                      //!<        Identification of the trigger that starts the operation
   struct {
      uint8_t rule:4;                   //!<        Condition for running next command: Rule for how to proceed
      uint8_t nSkip:4;                  //!<        Number of skips + 1 if the rule involves skipping. 0: same, 1: next, 2: skip next, ...
   } condition;
   uint8_t channel;                     //!< \brief Channel to use<br>
                                        //!<        0--39: BLE advertising/data channel index<br>
                                        //!<        60--207: Custom frequency; (2300 + <code>channel</code>) MHz<br>
                                        //!<        255: Use existing frequency<br>
                                        //!<        Others: <i>Reserved</i>
   struct {
      uint8_t init:7;                   //!< \brief If <code>bOverride</code> = 1 or custom frequency is used:<br>
                                        //!<        0: Do not use whitening<br>
                                        //!<        Other value: Initialization for 7-bit LFSR whitener
      uint8_t bOverride:1;              //!< \brief 0: Use default whitening for BLE advertising/data channels<br>
                                        //!<        1: Override whitening initialization with value of init
   } whitening;
   rfc_bleScannerPar_t *pParams;        //!<        Pointer to command specific parameter structure
   rfc_bleScannerOutput_t *pOutput;     //!<        Pointer to command specific output structure
} __RFC_STRUCT_ATTR;

//! @}

//! \addtogroup CMD_BLE_INITIATOR
//! @{
#define CMD_BLE_INITIATOR                                       0x1808
//! BLE Initiator Command
struct __RFC_STRUCT rfc_CMD_BLE_INITIATOR_s {
   uint16_t commandNo;                  //!<        The command ID number 0x1808
   uint16_t status;                     //!< \brief An integer telling the status of the command. This value is
                                        //!<        updated by the radio CPU during operation and may be read by the
                                        //!<        system CPU at any time.
   rfc_radioOp_t *pNextOp;              //!<        Pointer to the next operation to run after this operation is done
   ratmr_t startTime;                   //!<        Absolute or relative start time (depending on the value of <code>startTrigger</code>)
   struct {
      uint8_t triggerType:4;            //!<        The type of trigger
      uint8_t bEnaCmd:1;                //!< \brief 0: No alternative trigger command<br>
                                        //!<        1: CMD_TRIGGER can be used as an alternative trigger
      uint8_t triggerNo:2;              //!<        The trigger number of the CMD_TRIGGER command that triggers this action
      uint8_t pastTrig:1;               //!< \brief 0: A trigger in the past is never triggered, or for start of commands, give an error<br>
                                        //!<        1: A trigger in the past is triggered as soon as possible
   } startTrigger;                      //!<        Identification of the trigger that starts the operation
   struct {
      uint8_t rule:4;                   //!<        Condition for running next command: Rule for how to proceed
      uint8_t nSkip:4;                  //!<        Number of skips + 1 if the rule involves skipping. 0: same, 1: next, 2: skip next, ...
   } condition;
   uint8_t channel;                     //!< \brief Channel to use<br>
                                        //!<        0--39: BLE advertising/data channel index<br>
                                        //!<        60--207: Custom frequency; (2300 + <code>channel</code>) MHz<br>
                                        //!<        255: Use existing frequency<br>
                                        //!<        Others: <i>Reserved</i>
   struct {
      uint8_t init:7;                   //!< \brief If <code>bOverride</code> = 1 or custom frequency is used:<br>
                                        //!<        0: Do not use whitening<br>
                                        //!<        Other value: Initialization for 7-bit LFSR whitener
      uint8_t bOverride:1;              //!< \brief 0: Use default whitening for BLE advertising/data channels<br>
                                        //!<        1: Override whitening initialization with value of init
   } whitening;
   rfc_bleInitiatorPar_t *pParams;      //!<        Pointer to command specific parameter structure
   rfc_bleInitiatorOutput_t *pOutput;   //!<        Pointer to command specific output structure
} __RFC_STRUCT_ATTR;

//! @}

//! \addtogroup CMD_BLE_GENERIC_RX
//! @{
#define CMD_BLE_GENERIC_RX                                      0x1809
//! BLE Generic Receiver Command
struct __RFC_STRUCT rfc_CMD_BLE_GENERIC_RX_s {
   uint16_t commandNo;                  //!<        The command ID number 0x1809
   uint16_t status;                     //!< \brief An integer telling the status of the command. This value is
                                        //!<        updated by the radio CPU during operation and may be read by the
                                        //!<        system CPU at any time.
   rfc_radioOp_t *pNextOp;              //!<        Pointer to the next operation to run after this operation is done
   ratmr_t startTime;                   //!<        Absolute or relative start time (depending on the value of <code>startTrigger</code>)
   struct {
      uint8_t triggerType:4;            //!<        The type of trigger
      uint8_t bEnaCmd:1;                //!< \brief 0: No alternative trigger command<br>
                                        //!<        1: CMD_TRIGGER can be used as an alternative trigger
      uint8_t triggerNo:2;              //!<        The trigger number of the CMD_TRIGGER command that triggers this action
      uint8_t pastTrig:1;               //!< \brief 0: A trigger in the past is never triggered, or for start of commands, give an error<br>
                                        //!<        1: A trigger in the past is triggered as soon as possible
   } startTrigger;                      //!<        Identification of the trigger that starts the operation
   struct {
      uint8_t rule:4;                   //!<        Condition for running next command: Rule for how to proceed
      uint8_t nSkip:4;                  //!<        Number of skips + 1 if the rule involves skipping. 0: same, 1: next, 2: skip next, ...
   } condition;
   uint8_t channel;                     //!< \brief Channel to use<br>
                                        //!<        0--39: BLE advertising/data channel index<br>
                                        //!<        60--207: Custom frequency; (2300 + <code>channel</code>) MHz<br>
                                        //!<        255: Use existing frequency<br>
                                        //!<        Others: <i>Reserved</i>
   struct {
      uint8_t init:7;                   //!< \brief If <code>bOverride</code> = 1 or custom frequency is used:<br>
                                        //!<        0: Do not use whitening<br>
                                        //!<        Other value: Initialization for 7-bit LFSR whitener
      uint8_t bOverride:1;              //!< \brief 0: Use default whitening for BLE advertising/data channels<br>
                                        //!<        1: Override whitening initialization with value of init
   } whitening;
   rfc_bleGenericRxPar_t *pParams;      //!<        Pointer to command specific parameter structure
   rfc_bleGenericRxOutput_t *pOutput;   //!<        Pointer to command specific output structure
} __RFC_STRUCT_ATTR;

//! @}

//! \addtogroup CMD_BLE_TX_TEST
//! @{
#define CMD_BLE_TX_TEST                                         0x180A
//! BLE PHY Test Transmitter Command
struct __RFC_STRUCT rfc_CMD_BLE_TX_TEST_s {
   uint16_t commandNo;                  //!<        The command ID number 0x180A
   uint16_t status;                     //!< \brief An integer telling the status of the command. This value is
                                        //!<        updated by the radio CPU during operation and may be read by the
                                        //!<        system CPU at any time.
   rfc_radioOp_t *pNextOp;              //!<        Pointer to the next operation to run after this operation is done
   ratmr_t startTime;                   //!<        Absolute or relative start time (depending on the value of <code>startTrigger</code>)
   struct {
      uint8_t triggerType:4;            //!<        The type of trigger
      uint8_t bEnaCmd:1;                //!< \brief 0: No alternative trigger command<br>
                                        //!<        1: CMD_TRIGGER can be used as an alternative trigger
      uint8_t triggerNo:2;              //!<        The trigger number of the CMD_TRIGGER command that triggers this action
      uint8_t pastTrig:1;               //!< \brief 0: A trigger in the past is never triggered, or for start of commands, give an error<br>
                                        //!<        1: A trigger in the past is triggered as soon as possible
   } startTrigger;                      //!<        Identification of the trigger that starts the operation
   struct {
      uint8_t rule:4;                   //!<        Condition for running next command: Rule for how to proceed
      uint8_t nSkip:4;                  //!<        Number of skips + 1 if the rule involves skipping. 0: same, 1: next, 2: skip next, ...
   } condition;
   uint8_t channel;                     //!< \brief Channel to use<br>
                                        //!<        0--39: BLE advertising/data channel index<br>
                                        //!<        60--207: Custom frequency; (2300 + <code>channel</code>) MHz<br>
                                        //!<        255: Use existing frequency<br>
                                        //!<        Others: <i>Reserved</i>
   struct {
      uint8_t init:7;                   //!< \brief If <code>bOverride</code> = 1 or custom frequency is used:<br>
                                        //!<        0: Do not use whitening<br>
                                        //!<        Other value: Initialization for 7-bit LFSR whitener
      uint8_t bOverride:1;              //!< \brief 0: Use default whitening for BLE advertising/data channels<br>
                                        //!<        1: Override whitening initialization with value of init
   } whitening;
   rfc_bleTxTestPar_t *pParams;         //!<        Pointer to command specific parameter structure
   rfc_bleTxTestOutput_t *pOutput;      //!<        Pointer to command specific output structure
} __RFC_STRUCT_ATTR;

//! @}

//! \addtogroup CMD_BLE_ADV_PAYLOAD
//! @{
#define CMD_BLE_ADV_PAYLOAD                                     0x1001
//! BLE Update Advertising Payload Command
struct __RFC_STRUCT rfc_CMD_BLE_ADV_PAYLOAD_s {
   uint16_t commandNo;                  //!<        The command ID number 0x1001
   uint8_t payloadType;                 //!< \brief 0: Advertising data<br>
                                        //!<        1: Scan response data
   uint8_t newLen;                      //!<        Length of the new payload
   uint8_t* pNewData;                   //!<        Pointer to the buffer containing the new data
   rfc_bleAdvPar_t *pParams;            //!<        Pointer to the parameter structure to update
} __RFC_STRUCT_ATTR;

//! @}

//! \addtogroup CMD_BLE5_RADIO_SETUP
//! @{
#define CMD_BLE5_RADIO_SETUP                                    0x1820
//! Bluetooth 5 Radio Setup Command for all PHYs
struct __RFC_STRUCT rfc_CMD_BLE5_RADIO_SETUP_s {
   uint16_t commandNo;                  //!<        The command ID number 0x1820
   uint16_t status;                     //!< \brief An integer telling the status of the command. This value is
                                        //!<        updated by the radio CPU during operation and may be read by the
                                        //!<        system CPU at any time.
   rfc_radioOp_t *pNextOp;              //!<        Pointer to the next operation to run after this operation is done
   ratmr_t startTime;                   //!<        Absolute or relative start time (depending on the value of <code>startTrigger</code>)
   struct {
      uint8_t triggerType:4;            //!<        The type of trigger
      uint8_t bEnaCmd:1;                //!< \brief 0: No alternative trigger command<br>
                                        //!<        1: CMD_TRIGGER can be used as an alternative trigger
      uint8_t triggerNo:2;              //!<        The trigger number of the CMD_TRIGGER command that triggers this action
      uint8_t pastTrig:1;               //!< \brief 0: A trigger in the past is never triggered, or for start of commands, give an error<br>
                                        //!<        1: A trigger in the past is triggered as soon as possible
   } startTrigger;                      //!<        Identification of the trigger that starts the operation
   struct {
      uint8_t rule:4;                   //!<        Condition for running next command: Rule for how to proceed
      uint8_t nSkip:4;                  //!<        Number of skips + 1 if the rule involves skipping. 0: same, 1: next, 2: skip next, ...
   } condition;
   struct {
      uint8_t mainMode:2;               //!< \brief PHY to use for non-BLE commands:<br>
                                        //!<        0: 1 Mbps<br>
                                        //!<        1: 2 Mbps<br>
                                        //!<        2: Coded<br>
                                        //!<        3: <i>Reserved</i>
      uint8_t coding:1;                 //!< \brief Coding to use for TX if coded PHY is selected for non-BLE commands<br>
                                        //!<        0: S = 8 (125 kbps)<br>
                                        //!<        1: S = 2 (500 kbps)
   } defaultPhy;
   uint8_t __dummy0;
   struct {
      uint16_t frontEndMode:3;          //!< \brief 0x00: Differential mode<br>
                                        //!<        0x01: Single-ended mode RFP<br>
                                        //!<        0x02: Single-ended mode RFN<br>
                                        //!<        0x05 Single-ended mode RFP with external frontend control on RF pins (RFN and RXTX)<br>
                                        //!<        0x06 Single-ended mode RFN with external frontend control on RF pins (RFP and RXTX)<br>
                                        //!<        Others: <i>Reserved</i>
      uint16_t biasMode:1;              //!< \brief 0: Internal bias<br>
                                        //!<        1: External bias
      uint16_t analogCfgMode:6;         //!< \brief 0x00: Write analog configuration.<br>
                                        //!<        Required first time after boot and when changing frequency band
                                        //!<        or front-end configuration<br>
                                        //!<        0x2D: Keep analog configuration.<br>
                                        //!<        May be used after standby or when changing mode with the same frequency
                                        //!<        band and front-end configuration<br>
                                        //!<        Others: <i>Reserved</i>
      uint16_t bNoFsPowerUp:1;          //!< \brief 0: Power up frequency synth<br>
                                        //!<        1: Do not power up frequency synth
   } config;                            //!<        Configuration options
   uint16_t txPower;                    //!<        Default transmit power
   uint32_t* pRegOverrideCommon;        //!< \brief Pointer to a list of hardware and configuration registers to override during common
                                        //!<        initialization. If NULL, no override is used.
   uint32_t* pRegOverride1Mbps;         //!< \brief Pointer to a list of hardware and configuration registers to override when selecting
                                        //!<        1 Mbps PHY mode. If NULL, no override is used.
   uint32_t* pRegOverride2Mbps;         //!< \brief Pointer to a list of hardware and configuration registers to override when selecting
                                        //!<        2 Mbps PHY mode. If NULL, no override is used.
   uint32_t* pRegOverrideCoded;         //!< \brief Pointer to a list of hardware and configuration registers to override when selecting
                                        //!<        coded PHY mode. If NULL, no override is used.
} __RFC_STRUCT_ATTR;

//! @}

//! \addtogroup CMD_BLE5_SLAVE
//! @{
#define CMD_BLE5_SLAVE                                          0x1821
//! Bluetooth 5 Slave Command
struct __RFC_STRUCT rfc_CMD_BLE5_SLAVE_s {
   uint16_t commandNo;                  //!<        The command ID number 0x1821
   uint16_t status;                     //!< \brief An integer telling the status of the command. This value is
                                        //!<        updated by the radio CPU during operation and may be read by the
                                        //!<        system CPU at any time.
   rfc_radioOp_t *pNextOp;              //!<        Pointer to the next operation to run after this operation is done
   ratmr_t startTime;                   //!<        Absolute or relative start time (depending on the value of <code>startTrigger</code>)
   struct {
      uint8_t triggerType:4;            //!<        The type of trigger
      uint8_t bEnaCmd:1;                //!< \brief 0: No alternative trigger command<br>
                                        //!<        1: CMD_TRIGGER can be used as an alternative trigger
      uint8_t triggerNo:2;              //!<        The trigger number of the CMD_TRIGGER command that triggers this action
      uint8_t pastTrig:1;               //!< \brief 0: A trigger in the past is never triggered, or for start of commands, give an error<br>
                                        //!<        1: A trigger in the past is triggered as soon as possible
   } startTrigger;                      //!<        Identification of the trigger that starts the operation
   struct {
      uint8_t rule:4;                   //!<        Condition for running next command: Rule for how to proceed
      uint8_t nSkip:4;                  //!<        Number of skips + 1 if the rule involves skipping. 0: same, 1: next, 2: skip next, ...
   } condition;
   uint8_t channel;                     //!< \brief Channel to use<br>
                                        //!<        0--39: BLE advertising/data channel index<br>
                                        //!<        60--207: Custom frequency; (2300 + <code>channel</code>) MHz<br>
                                        //!<        255: Use existing frequency<br>
                                        //!<        Others: <i>Reserved</i>
   struct {
      uint8_t init:7;                   //!< \brief If <code>bOverride</code> = 1 or custom frequency is used:<br>
                                        //!<        0: Do not use whitening<br>
                                        //!<        Other value: Initialization for 7-bit LFSR whitener
      uint8_t bOverride:1;              //!< \brief 0: Use default whitening for BLE advertising/data channels<br>
                                        //!<        1: Override whitening initialization with value of init
   } whitening;
   struct {
      uint8_t mainMode:2;               //!< \brief PHY to use:<br>
                                        //!<        0: 1 Mbps<br>
                                        //!<        1: 2 Mbps<br>
                                        //!<        2: Coded<br>
                                        //!<        3: <i>Reserved</i>
      uint8_t coding:6;                 //!< \brief Coding to use for TX if coded PHY is selected.
                                        //!<        See the Technical Reference Manual for details.
   } phyMode;
   uint8_t rangeDelay;                  //!<        Number of RAT ticks to add to the listening time after T_IFS
   uint16_t txPower;                    //!< \brief Transmit power to use (overrides the one given in radio setup).
                                        //!<        0x0000: Use default TX power.
   rfc_ble5SlavePar_t *pParams;         //!<        Pointer to command specific parameter structure
   rfc_bleMasterSlaveOutput_t *pOutput; //!<        Pointer to command specific output structure
} __RFC_STRUCT_ATTR;

//! @}

//! \addtogroup CMD_BLE5_MASTER
//! @{
#define CMD_BLE5_MASTER                                         0x1822
//! Bluetooth 5 Master Command
struct __RFC_STRUCT rfc_CMD_BLE5_MASTER_s {
   uint16_t commandNo;                  //!<        The command ID number 0x1822
   uint16_t status;                     //!< \brief An integer telling the status of the command. This value is
                                        //!<        updated by the radio CPU during operation and may be read by the
                                        //!<        system CPU at any time.
   rfc_radioOp_t *pNextOp;              //!<        Pointer to the next operation to run after this operation is done
   ratmr_t startTime;                   //!<        Absolute or relative start time (depending on the value of <code>startTrigger</code>)
   struct {
      uint8_t triggerType:4;            //!<        The type of trigger
      uint8_t bEnaCmd:1;                //!< \brief 0: No alternative trigger command<br>
                                        //!<        1: CMD_TRIGGER can be used as an alternative trigger
      uint8_t triggerNo:2;              //!<        The trigger number of the CMD_TRIGGER command that triggers this action
      uint8_t pastTrig:1;               //!< \brief 0: A trigger in the past is never triggered, or for start of commands, give an error<br>
                                        //!<        1: A trigger in the past is triggered as soon as possible
   } startTrigger;                      //!<        Identification of the trigger that starts the operation
   struct {
      uint8_t rule:4;                   //!<        Condition for running next command: Rule for how to proceed
      uint8_t nSkip:4;                  //!<        Number of skips + 1 if the rule involves skipping. 0: same, 1: next, 2: skip next, ...
   } condition;
   uint8_t channel;                     //!< \brief Channel to use<br>
                                        //!<        0--39: BLE advertising/data channel index<br>
                                        //!<        60--207: Custom frequency; (2300 + <code>channel</code>) MHz<br>
                                        //!<        255: Use existing frequency<br>
                                        //!<        Others: <i>Reserved</i>
   struct {
      uint8_t init:7;                   //!< \brief If <code>bOverride</code> = 1 or custom frequency is used:<br>
                                        //!<        0: Do not use whitening<br>
                                        //!<        Other value: Initialization for 7-bit LFSR whitener
      uint8_t bOverride:1;              //!< \brief 0: Use default whitening for BLE advertising/data channels<br>
                                        //!<        1: Override whitening initialization with value of init
   } whitening;
   struct {
      uint8_t mainMode:2;               //!< \brief PHY to use:<br>
                                        //!<        0: 1 Mbps<br>
                                        //!<        1: 2 Mbps<br>
                                        //!<        2: Coded<br>
                                        //!<        3: <i>Reserved</i>
      uint8_t coding:6;                 //!< \brief Coding to use for TX if coded PHY is selected.
                                        //!<        See the Technical Reference Manual for details.
   } phyMode;
   uint8_t rangeDelay;                  //!<        Number of RAT ticks to add to the listening time after T_IFS
   uint16_t txPower;                    //!< \brief Transmit power to use (overrides the one given in radio setup).
                                        //!<        0x0000: Use default TX power.
   rfc_ble5MasterPar_t *pParams;        //!<        Pointer to command specific parameter structure
   rfc_bleMasterSlaveOutput_t *pOutput; //!<        Pointer to command specific output structure
} __RFC_STRUCT_ATTR;

//! @}

//! \addtogroup CMD_BLE5_ADV_EXT
//! @{
#define CMD_BLE5_ADV_EXT                                        0x1823
//! Bluetooth 5 Extended Advertiser Command
struct __RFC_STRUCT rfc_CMD_BLE5_ADV_EXT_s {
   uint16_t commandNo;                  //!<        The command ID number 0x1823
   uint16_t status;                     //!< \brief An integer telling the status of the command. This value is
                                        //!<        updated by the radio CPU during operation and may be read by the
                                        //!<        system CPU at any time.
   rfc_radioOp_t *pNextOp;              //!<        Pointer to the next operation to run after this operation is done
   ratmr_t startTime;                   //!<        Absolute or relative start time (depending on the value of <code>startTrigger</code>)
   struct {
      uint8_t triggerType:4;            //!<        The type of trigger
      uint8_t bEnaCmd:1;                //!< \brief 0: No alternative trigger command<br>
                                        //!<        1: CMD_TRIGGER can be used as an alternative trigger
      uint8_t triggerNo:2;              //!<        The trigger number of the CMD_TRIGGER command that triggers this action
      uint8_t pastTrig:1;               //!< \brief 0: A trigger in the past is never triggered, or for start of commands, give an error<br>
                                        //!<        1: A trigger in the past is triggered as soon as possible
   } startTrigger;                      //!<        Identification of the trigger that starts the operation
   struct {
      uint8_t rule:4;                   //!<        Condition for running next command: Rule for how to proceed
      uint8_t nSkip:4;                  //!<        Number of skips + 1 if the rule involves skipping. 0: same, 1: next, 2: skip next, ...
   } condition;
   uint8_t channel;                     //!< \brief Channel to use<br>
                                        //!<        0--39: BLE advertising/data channel index<br>
                                        //!<        60--207: Custom frequency; (2300 + <code>channel</code>) MHz<br>
                                        //!<        255: Use existing frequency<br>
                                        //!<        Others: <i>Reserved</i>
   struct {
      uint8_t init:7;                   //!< \brief If <code>bOverride</code> = 1 or custom frequency is used:<br>
                                        //!<        0: Do not use whitening<br>
                                        //!<        Other value: Initialization for 7-bit LFSR whitener
      uint8_t bOverride:1;              //!< \brief 0: Use default whitening for BLE advertising/data channels<br>
                                        //!<        1: Override whitening initialization with value of init
   } whitening;
   struct {
      uint8_t mainMode:2;               //!< \brief PHY to use:<br>
                                        //!<        0: 1 Mbps<br>
                                        //!<        1: 2 Mbps<br>
                                        //!<        2: Coded<br>
                                        //!<        3: <i>Reserved</i>
      uint8_t coding:6;                 //!< \brief Coding to use for TX if coded PHY is selected.
                                        //!<        See the Technical Reference Manual for details.
   } phyMode;
   uint8_t rangeDelay;                  //!<        Number of RAT ticks to add to the listening time after T_IFS
   uint16_t txPower;                    //!< \brief Transmit power to use (overrides the one given in radio setup).
                                        //!<        0x0000: Use default TX power.
   rfc_ble5AdvExtPar_t *pParams;        //!<        Pointer to command specific parameter structure
   rfc_bleAdvOutput_t *pOutput;         //!<        Pointer to command specific output structure
} __RFC_STRUCT_ATTR;

//! @}

//! \addtogroup CMD_BLE5_ADV_AUX
//! @{
#define CMD_BLE5_ADV_AUX                                        0x1824
//! Bluetooth 5 Secondary Channel Advertiser Command
struct __RFC_STRUCT rfc_CMD_BLE5_ADV_AUX_s {
   uint16_t commandNo;                  //!<        The command ID number 0x1824
   uint16_t status;                     //!< \brief An integer telling the status of the command. This value is
                                        //!<        updated by the radio CPU during operation and may be read by the
                                        //!<        system CPU at any time.
   rfc_radioOp_t *pNextOp;              //!<        Pointer to the next operation to run after this operation is done
   ratmr_t startTime;                   //!<        Absolute or relative start time (depending on the value of <code>startTrigger</code>)
   struct {
      uint8_t triggerType:4;            //!<        The type of trigger
      uint8_t bEnaCmd:1;                //!< \brief 0: No alternative trigger command<br>
                                        //!<        1: CMD_TRIGGER can be used as an alternative trigger
      uint8_t triggerNo:2;              //!<        The trigger number of the CMD_TRIGGER command that triggers this action
      uint8_t pastTrig:1;               //!< \brief 0: A trigger in the past is never triggered, or for start of commands, give an error<br>
                                        //!<        1: A trigger in the past is triggered as soon as possible
   } startTrigger;                      //!<        Identification of the trigger that starts the operation
   struct {
      uint8_t rule:4;                   //!<        Condition for running next command: Rule for how to proceed
      uint8_t nSkip:4;                  //!<        Number of skips + 1 if the rule involves skipping. 0: same, 1: next, 2: skip next, ...
   } condition;
   uint8_t channel;                     //!< \brief Channel to use<br>
                                        //!<        0--39: BLE advertising/data channel index<br>
                                        //!<        60--207: Custom frequency; (2300 + <code>channel</code>) MHz<br>
                                        //!<        255: Use existing frequency<br>
                                        //!<        Others: <i>Reserved</i>
   struct {
      uint8_t init:7;                   //!< \brief If <code>bOverride</code> = 1 or custom frequency is used:<br>
                                        //!<        0: Do not use whitening<br>
                                        //!<        Other value: Initialization for 7-bit LFSR whitener
      uint8_t bOverride:1;              //!< \brief 0: Use default whitening for BLE advertising/data channels<br>
                                        //!<        1: Override whitening initialization with value of init
   } whitening;
   struct {
      uint8_t mainMode:2;               //!< \brief PHY to use:<br>
                                        //!<        0: 1 Mbps<br>
                                        //!<        1: 2 Mbps<br>
                                        //!<        2: Coded<br>
                                        //!<        3: <i>Reserved</i>
      uint8_t coding:6;                 //!< \brief Coding to use for TX if coded PHY is selected.
                                        //!<        See the Technical Reference Manual for details.
   } phyMode;
   uint8_t rangeDelay;                  //!<        Number of RAT ticks to add to the listening time after T_IFS
   uint16_t txPower;                    //!< \brief Transmit power to use (overrides the one given in radio setup).
                                        //!<        0x0000: Use default TX power.
   rfc_ble5AdvAuxPar_t *pParams;        //!<        Pointer to command specific parameter structure
   rfc_bleAdvOutput_t *pOutput;         //!<        Pointer to command specific output structure
} __RFC_STRUCT_ATTR;

//! @}

//! \addtogroup CMD_BLE5_SCANNER
//! @{
#define CMD_BLE5_SCANNER                                        0x1827
//! Bluetooth 5 Scanner Command
struct __RFC_STRUCT rfc_CMD_BLE5_SCANNER_s {
   uint16_t commandNo;                  //!<        The command ID number 0x1827
   uint16_t status;                     //!< \brief An integer telling the status of the command. This value is
                                        //!<        updated by the radio CPU during operation and may be read by the
                                        //!<        system CPU at any time.
   rfc_radioOp_t *pNextOp;              //!<        Pointer to the next operation to run after this operation is done
   ratmr_t startTime;                   //!<        Absolute or relative start time (depending on the value of <code>startTrigger</code>)
   struct {
      uint8_t triggerType:4;            //!<        The type of trigger
      uint8_t bEnaCmd:1;                //!< \brief 0: No alternative trigger command<br>
                                        //!<        1: CMD_TRIGGER can be used as an alternative trigger
      uint8_t triggerNo:2;              //!<        The trigger number of the CMD_TRIGGER command that triggers this action
      uint8_t pastTrig:1;               //!< \brief 0: A trigger in the past is never triggered, or for start of commands, give an error<br>
                                        //!<        1: A trigger in the past is triggered as soon as possible
   } startTrigger;                      //!<        Identification of the trigger that starts the operation
   struct {
      uint8_t rule:4;                   //!<        Condition for running next command: Rule for how to proceed
      uint8_t nSkip:4;                  //!<        Number of skips + 1 if the rule involves skipping. 0: same, 1: next, 2: skip next, ...
   } condition;
   uint8_t channel;                     //!< \brief Channel to use<br>
                                        //!<        0--39: BLE advertising/data channel index<br>
                                        //!<        60--207: Custom frequency; (2300 + <code>channel</code>) MHz<br>
                                        //!<        255: Use existing frequency<br>
                                        //!<        Others: <i>Reserved</i>
   struct {
      uint8_t init:7;                   //!< \brief If <code>bOverride</code> = 1 or custom frequency is used:<br>
                                        //!<        0: Do not use whitening<br>
                                        //!<        Other value: Initialization for 7-bit LFSR whitener
      uint8_t bOverride:1;              //!< \brief 0: Use default whitening for BLE advertising/data channels<br>
                                        //!<        1: Override whitening initialization with value of init
   } whitening;
   struct {
      uint8_t mainMode:2;               //!< \brief PHY to use:<br>
                                        //!<        0: 1 Mbps<br>
                                        //!<        1: 2 Mbps<br>
                                        //!<        2: Coded<br>
                                        //!<        3: <i>Reserved</i>
      uint8_t coding:6;                 //!< \brief Coding to use for TX if coded PHY is selected.
                                        //!<        See the Technical Reference Manual for details.
   } phyMode;
   uint8_t rangeDelay;                  //!<        Number of RAT ticks to add to the listening time after T_IFS
   uint16_t txPower;                    //!< \brief Transmit power to use (overrides the one given in radio setup).
                                        //!<        0x0000: Use default TX power.
   rfc_ble5ScannerPar_t *pParams;       //!<        Pointer to command specific parameter structure
   rfc_ble5ScanInitOutput_t *pOutput;   //!<        Pointer to command specific output structure
} __RFC_STRUCT_ATTR;

//! @}

//! \addtogroup CMD_BLE5_INITIATOR
//! @{
#define CMD_BLE5_INITIATOR                                      0x1828
//! Bluetooth 5 Initiator Command
struct __RFC_STRUCT rfc_CMD_BLE5_INITIATOR_s {
   uint16_t commandNo;                  //!<        The command ID number 0x1828
   uint16_t status;                     //!< \brief An integer telling the status of the command. This value is
                                        //!<        updated by the radio CPU during operation and may be read by the
                                        //!<        system CPU at any time.
   rfc_radioOp_t *pNextOp;              //!<        Pointer to the next operation to run after this operation is done
   ratmr_t startTime;                   //!<        Absolute or relative start time (depending on the value of <code>startTrigger</code>)
   struct {
      uint8_t triggerType:4;            //!<        The type of trigger
      uint8_t bEnaCmd:1;                //!< \brief 0: No alternative trigger command<br>
                                        //!<        1: CMD_TRIGGER can be used as an alternative trigger
      uint8_t triggerNo:2;              //!<        The trigger number of the CMD_TRIGGER command that triggers this action
      uint8_t pastTrig:1;               //!< \brief 0: A trigger in the past is never triggered, or for start of commands, give an error<br>
                                        //!<        1: A trigger in the past is triggered as soon as possible
   } startTrigger;                      //!<        Identification of the trigger that starts the operation
   struct {
      uint8_t rule:4;                   //!<        Condition for running next command: Rule for how to proceed
      uint8_t nSkip:4;                  //!<        Number of skips + 1 if the rule involves skipping. 0: same, 1: next, 2: skip next, ...
   } condition;
   uint8_t channel;                     //!< \brief Channel to use<br>
                                        //!<        0--39: BLE advertising/data channel index<br>
                                        //!<        60--207: Custom frequency; (2300 + <code>channel</code>) MHz<br>
                                        //!<        255: Use existing frequency<br>
                                        //!<        Others: <i>Reserved</i>
   struct {
      uint8_t init:7;                   //!< \brief If <code>bOverride</code> = 1 or custom frequency is used:<br>
                                        //!<        0: Do not use whitening<br>
                                        //!<        Other value: Initialization for 7-bit LFSR whitener
      uint8_t bOverride:1;              //!< \brief 0: Use default whitening for BLE advertising/data channels<br>
                                        //!<        1: Override whitening initialization with value of init
   } whitening;
   struct {
      uint8_t mainMode:2;               //!< \brief PHY to use:<br>
                                        //!<        0: 1 Mbps<br>
                                        //!<        1: 2 Mbps<br>
                                        //!<        2: Coded<br>
                                        //!<        3: <i>Reserved</i>
      uint8_t coding:6;                 //!< \brief Coding to use for TX if coded PHY is selected.
                                        //!<        See the Technical Reference Manual for details.
   } phyMode;
   uint8_t rangeDelay;                  //!<        Number of RAT ticks to add to the listening time after T_IFS
   uint16_t txPower;                    //!< \brief Transmit power to use (overrides the one given in radio setup).
                                        //!<        0x0000: Use default TX power.
   rfc_ble5InitiatorPar_t *pParams;     //!<        Pointer to command specific parameter structure
   rfc_ble5ScanInitOutput_t *pOutput;   //!<        Pointer to command specific output structure
} __RFC_STRUCT_ATTR;

//! @}

//! \addtogroup CMD_BLE5_GENERIC_RX
//! @{
#define CMD_BLE5_GENERIC_RX                                     0x1829
//! Bluetooth 5 Generic Receiver Command
struct __RFC_STRUCT rfc_CMD_BLE5_GENERIC_RX_s {
   uint16_t commandNo;                  //!<        The command ID number 0x1829
   uint16_t status;                     //!< \brief An integer telling the status of the command. This value is
                                        //!<        updated by the radio CPU during operation and may be read by the
                                        //!<        system CPU at any time.
   rfc_radioOp_t *pNextOp;              //!<        Pointer to the next operation to run after this operation is done
   ratmr_t startTime;                   //!<        Absolute or relative start time (depending on the value of <code>startTrigger</code>)
   struct {
      uint8_t triggerType:4;            //!<        The type of trigger
      uint8_t bEnaCmd:1;                //!< \brief 0: No alternative trigger command<br>
                                        //!<        1: CMD_TRIGGER can be used as an alternative trigger
      uint8_t triggerNo:2;              //!<        The trigger number of the CMD_TRIGGER command that triggers this action
      uint8_t pastTrig:1;               //!< \brief 0: A trigger in the past is never triggered, or for start of commands, give an error<br>
                                        //!<        1: A trigger in the past is triggered as soon as possible
   } startTrigger;                      //!<        Identification of the trigger that starts the operation
   struct {
      uint8_t rule:4;                   //!<        Condition for running next command: Rule for how to proceed
      uint8_t nSkip:4;                  //!<        Number of skips + 1 if the rule involves skipping. 0: same, 1: next, 2: skip next, ...
   } condition;
   uint8_t channel;                     //!< \brief Channel to use<br>
                                        //!<        0--39: BLE advertising/data channel index<br>
                                        //!<        60--207: Custom frequency; (2300 + <code>channel</code>) MHz<br>
                                        //!<        255: Use existing frequency<br>
                                        //!<        Others: <i>Reserved</i>
   struct {
      uint8_t init:7;                   //!< \brief If <code>bOverride</code> = 1 or custom frequency is used:<br>
                                        //!<        0: Do not use whitening<br>
                                        //!<        Other value: Initialization for 7-bit LFSR whitener
      uint8_t bOverride:1;              //!< \brief 0: Use default whitening for BLE advertising/data channels<br>
                                        //!<        1: Override whitening initialization with value of init
   } whitening;
   struct {
      uint8_t mainMode:2;               //!< \brief PHY to use:<br>
                                        //!<        0: 1 Mbps<br>
                                        //!<        1: 2 Mbps<br>
                                        //!<        2: Coded<br>
                                        //!<        3: <i>Reserved</i>
      uint8_t coding:6;                 //!< \brief Coding to use for TX if coded PHY is selected.
                                        //!<        See the Technical Reference Manual for details.
   } phyMode;
   uint8_t rangeDelay;                  //!<        Number of RAT ticks to add to the listening time after T_IFS
   uint16_t txPower;                    //!< \brief Transmit power to use (overrides the one given in radio setup).
                                        //!<        0x0000: Use default TX power.
   rfc_bleGenericRxPar_t *pParams;      //!<        Pointer to command specific parameter structure
   rfc_bleGenericRxOutput_t *pOutput;   //!<        Pointer to command specific output structure
} __RFC_STRUCT_ATTR;

//! @}

//! \addtogroup CMD_BLE5_TX_TEST
//! @{
#define CMD_BLE5_TX_TEST                                        0x182A
//! Bluetooth 5 PHY Test Transmitter Command
struct __RFC_STRUCT rfc_CMD_BLE5_TX_TEST_s {
   uint16_t commandNo;                  //!<        The command ID number 0x182A
   uint16_t status;                     //!< \brief An integer telling the status of the command. This value is
                                        //!<        updated by the radio CPU during operation and may be read by the
                                        //!<        system CPU at any time.
   rfc_radioOp_t *pNextOp;              //!<        Pointer to the next operation to run after this operation is done
   ratmr_t startTime;                   //!<        Absolute or relative start time (depending on the value of <code>startTrigger</code>)
   struct {
      uint8_t triggerType:4;            //!<        The type of trigger
      uint8_t bEnaCmd:1;                //!< \brief 0: No alternative trigger command<br>
                                        //!<        1: CMD_TRIGGER can be used as an alternative trigger
      uint8_t triggerNo:2;              //!<        The trigger number of the CMD_TRIGGER command that triggers this action
      uint8_t pastTrig:1;               //!< \brief 0: A trigger in the past is never triggered, or for start of commands, give an error<br>
                                        //!<        1: A trigger in the past is triggered as soon as possible
   } startTrigger;                      //!<        Identification of the trigger that starts the operation
   struct {
      uint8_t rule:4;                   //!<        Condition for running next command: Rule for how to proceed
      uint8_t nSkip:4;                  //!<        Number of skips + 1 if the rule involves skipping. 0: same, 1: next, 2: skip next, ...
   } condition;
   uint8_t channel;                     //!< \brief Channel to use<br>
                                        //!<        0--39: BLE advertising/data channel index<br>
                                        //!<        60--207: Custom frequency; (2300 + <code>channel</code>) MHz<br>
                                        //!<        255: Use existing frequency<br>
                                        //!<        Others: <i>Reserved</i>
   struct {
      uint8_t init:7;                   //!< \brief If <code>bOverride</code> = 1 or custom frequency is used:<br>
                                        //!<        0: Do not use whitening<br>
                                        //!<        Other value: Initialization for 7-bit LFSR whitener
      uint8_t bOverride:1;              //!< \brief 0: Use default whitening for BLE advertising/data channels<br>
                                        //!<        1: Override whitening initialization with value of init
   } whitening;
   struct {
      uint8_t mainMode:2;               //!< \brief PHY to use:<br>
                                        //!<        0: 1 Mbps<br>
                                        //!<        1: 2 Mbps<br>
                                        //!<        2: Coded<br>
                                        //!<        3: <i>Reserved</i>
      uint8_t coding:6;                 //!< \brief Coding to use for TX if coded PHY is selected.
                                        //!<        See the Technical Reference Manual for details.
   } phyMode;
   uint8_t rangeDelay;                  //!<        Number of RAT ticks to add to the listening time after T_IFS
   uint16_t txPower;                    //!< \brief Transmit power to use (overrides the one given in radio setup).
                                        //!<        0x0000: Use default TX power.
   rfc_bleTxTestPar_t *pParams;         //!<        Pointer to command specific parameter structure
   rfc_bleTxTestOutput_t *pOutput;      //!<        Pointer to command specific output structure
} __RFC_STRUCT_ATTR;

//! @}

//! \addtogroup CMD_BLE5_ADV
//! @{
#define CMD_BLE5_ADV                                            0x182B
//! Bluetooth 5 Connectable Undirected Advertiser Command
struct __RFC_STRUCT rfc_CMD_BLE5_ADV_s {
   uint16_t commandNo;                  //!<        The command ID number 0x182B
   uint16_t status;                     //!< \brief An integer telling the status of the command. This value is
                                        //!<        updated by the radio CPU during operation and may be read by the
                                        //!<        system CPU at any time.
   rfc_radioOp_t *pNextOp;              //!<        Pointer to the next operation to run after this operation is done
   ratmr_t startTime;                   //!<        Absolute or relative start time (depending on the value of <code>startTrigger</code>)
   struct {
      uint8_t triggerType:4;            //!<        The type of trigger
      uint8_t bEnaCmd:1;                //!< \brief 0: No alternative trigger command<br>
                                        //!<        1: CMD_TRIGGER can be used as an alternative trigger
      uint8_t triggerNo:2;              //!<        The trigger number of the CMD_TRIGGER command that triggers this action
      uint8_t pastTrig:1;               //!< \brief 0: A trigger in the past is never triggered, or for start of commands, give an error<br>
                                        //!<        1: A trigger in the past is triggered as soon as possible
   } startTrigger;                      //!<        Identification of the trigger that starts the operation
   struct {
      uint8_t rule:4;                   //!<        Condition for running next command: Rule for how to proceed
      uint8_t nSkip:4;                  //!<        Number of skips + 1 if the rule involves skipping. 0: same, 1: next, 2: skip next, ...
   } condition;
   uint8_t channel;                     //!< \brief Channel to use<br>
                                        //!<        0--39: BLE advertising/data channel index<br>
                                        //!<        60--207: Custom frequency; (2300 + <code>channel</code>) MHz<br>
                                        //!<        255: Use existing frequency<br>
                                        //!<        Others: <i>Reserved</i>
   struct {
      uint8_t init:7;                   //!< \brief If <code>bOverride</code> = 1 or custom frequency is used:<br>
                                        //!<        0: Do not use whitening<br>
                                        //!<        Other value: Initialization for 7-bit LFSR whitener
      uint8_t bOverride:1;              //!< \brief 0: Use default whitening for BLE advertising/data channels<br>
                                        //!<        1: Override whitening initialization with value of init
   } whitening;
   struct {
      uint8_t mainMode:2;               //!< \brief PHY to use:<br>
                                        //!<        0: 1 Mbps<br>
                                        //!<        1: 2 Mbps<br>
                                        //!<        2: Coded<br>
                                        //!<        3: <i>Reserved</i>
      uint8_t coding:6;                 //!< \brief Coding to use for TX if coded PHY is selected.
                                        //!<        See the Technical Reference Manual for details.
   } phyMode;
   uint8_t rangeDelay;                  //!<        Number of RAT ticks to add to the listening time after T_IFS
   uint16_t txPower;                    //!< \brief Transmit power to use (overrides the one given in radio setup).
                                        //!<        0x0000: Use default TX power.
   rfc_bleAdvPar_t *pParams;            //!<        Pointer to command specific parameter structure
   rfc_bleAdvOutput_t *pOutput;         //!<        Pointer to command specific output structure
} __RFC_STRUCT_ATTR;

//! @}

//! \addtogroup CMD_BLE5_ADV_DIR
//! @{
#define CMD_BLE5_ADV_DIR                                        0x182C
//! Bluetooth 5 Connectable Directed Advertiser Command
struct __RFC_STRUCT rfc_CMD_BLE5_ADV_DIR_s {
   uint16_t commandNo;                  //!<        The command ID number 0x182C
   uint16_t status;                     //!< \brief An integer telling the status of the command. This value is
                                        //!<        updated by the radio CPU during operation and may be read by the
                                        //!<        system CPU at any time.
   rfc_radioOp_t *pNextOp;              //!<        Pointer to the next operation to run after this operation is done
   ratmr_t startTime;                   //!<        Absolute or relative start time (depending on the value of <code>startTrigger</code>)
   struct {
      uint8_t triggerType:4;            //!<        The type of trigger
      uint8_t bEnaCmd:1;                //!< \brief 0: No alternative trigger command<br>
                                        //!<        1: CMD_TRIGGER can be used as an alternative trigger
      uint8_t triggerNo:2;              //!<        The trigger number of the CMD_TRIGGER command that triggers this action
      uint8_t pastTrig:1;               //!< \brief 0: A trigger in the past is never triggered, or for start of commands, give an error<br>
                                        //!<        1: A trigger in the past is triggered as soon as possible
   } startTrigger;                      //!<        Identification of the trigger that starts the operation
   struct {
      uint8_t rule:4;                   //!<        Condition for running next command: Rule for how to proceed
      uint8_t nSkip:4;                  //!<        Number of skips + 1 if the rule involves skipping. 0: same, 1: next, 2: skip next, ...
   } condition;
   uint8_t channel;                     //!< \brief Channel to use<br>
                                        //!<        0--39: BLE advertising/data channel index<br>
                                        //!<        60--207: Custom frequency; (2300 + <code>channel</code>) MHz<br>
                                        //!<        255: Use existing frequency<br>
                                        //!<        Others: <i>Reserved</i>
   struct {
      uint8_t init:7;                   //!< \brief If <code>bOverride</code> = 1 or custom frequency is used:<br>
                                        //!<        0: Do not use whitening<br>
                                        //!<        Other value: Initialization for 7-bit LFSR whitener
      uint8_t bOverride:1;              //!< \brief 0: Use default whitening for BLE advertising/data channels<br>
                                        //!<        1: Override whitening initialization with value of init
   } whitening;
   struct {
      uint8_t mainMode:2;               //!< \brief PHY to use:<br>
                                        //!<        0: 1 Mbps<br>
                                        //!<        1: 2 Mbps<br>
                                        //!<        2: Coded<br>
                                        //!<        3: <i>Reserved</i>
      uint8_t coding:6;                 //!< \brief Coding to use for TX if coded PHY is selected.
                                        //!<        See the Technical Reference Manual for details.
   } phyMode;
   uint8_t rangeDelay;                  //!<        Number of RAT ticks to add to the listening time after T_IFS
   uint16_t txPower;                    //!< \brief Transmit power to use (overrides the one given in radio setup).
                                        //!<        0x0000: Use default TX power.
   rfc_bleAdvPar_t *pParams;            //!<        Pointer to command specific parameter structure
   rfc_bleAdvOutput_t *pOutput;         //!<        Pointer to command specific output structure
} __RFC_STRUCT_ATTR;

//! @}

//! \addtogroup CMD_BLE5_ADV_NC
//! @{
#define CMD_BLE5_ADV_NC                                         0x182D
//! Bluetooth 5 Non-Connectable Advertiser Command
struct __RFC_STRUCT rfc_CMD_BLE5_ADV_NC_s {
   uint16_t commandNo;                  //!<        The command ID number 0x182D
   uint16_t status;                     //!< \brief An integer telling the status of the command. This value is
                                        //!<        updated by the radio CPU during operation and may be read by the
                                        //!<        system CPU at any time.
   rfc_radioOp_t *pNextOp;              //!<        Pointer to the next operation to run after this operation is done
   ratmr_t startTime;                   //!<        Absolute or relative start time (depending on the value of <code>startTrigger</code>)
   struct {
      uint8_t triggerType:4;            //!<        The type of trigger
      uint8_t bEnaCmd:1;                //!< \brief 0: No alternative trigger command<br>
                                        //!<        1: CMD_TRIGGER can be used as an alternative trigger
      uint8_t triggerNo:2;              //!<        The trigger number of the CMD_TRIGGER command that triggers this action
      uint8_t pastTrig:1;               //!< \brief 0: A trigger in the past is never triggered, or for start of commands, give an error<br>
                                        //!<        1: A trigger in the past is triggered as soon as possible
   } startTrigger;                      //!<        Identification of the trigger that starts the operation
   struct {
      uint8_t rule:4;                   //!<        Condition for running next command: Rule for how to proceed
      uint8_t nSkip:4;                  //!<        Number of skips + 1 if the rule involves skipping. 0: same, 1: next, 2: skip next, ...
   } condition;
   uint8_t channel;                     //!< \brief Channel to use<br>
                                        //!<        0--39: BLE advertising/data channel index<br>
                                        //!<        60--207: Custom frequency; (2300 + <code>channel</code>) MHz<br>
                                        //!<        255: Use existing frequency<br>
                                        //!<        Others: <i>Reserved</i>
   struct {
      uint8_t init:7;                   //!< \brief If <code>bOverride</code> = 1 or custom frequency is used:<br>
                                        //!<        0: Do not use whitening<br>
                                        //!<        Other value: Initialization for 7-bit LFSR whitener
      uint8_t bOverride:1;              //!< \brief 0: Use default whitening for BLE advertising/data channels<br>
                                        //!<        1: Override whitening initialization with value of init
   } whitening;
   struct {
      uint8_t mainMode:2;               //!< \brief PHY to use:<br>
                                        //!<        0: 1 Mbps<br>
                                        //!<        1: 2 Mbps<br>
                                        //!<        2: Coded<br>
                                        //!<        3: <i>Reserved</i>
      uint8_t coding:6;                 //!< \brief Coding to use for TX if coded PHY is selected.
                                        //!<        See the Technical Reference Manual for details.
   } phyMode;
   uint8_t rangeDelay;                  //!<        Number of RAT ticks to add to the listening time after T_IFS
   uint16_t txPower;                    //!< \brief Transmit power to use (overrides the one given in radio setup).
                                        //!<        0x0000: Use default TX power.
   rfc_bleAdvPar_t *pParams;            //!<        Pointer to command specific parameter structure
   rfc_bleAdvOutput_t *pOutput;         //!<        Pointer to command specific output structure
} __RFC_STRUCT_ATTR;

//! @}

//! \addtogroup CMD_BLE5_ADV_SCAN
//! @{
#define CMD_BLE5_ADV_SCAN                                       0x182E
//! Bluetooth 5 Scannable Undirected Advertiser Command
struct __RFC_STRUCT rfc_CMD_BLE5_ADV_SCAN_s {
   uint16_t commandNo;                  //!<        The command ID number 0x182E
   uint16_t status;                     //!< \brief An integer telling the status of the command. This value is
                                        //!<        updated by the radio CPU during operation and may be read by the
                                        //!<        system CPU at any time.
   rfc_radioOp_t *pNextOp;              //!<        Pointer to the next operation to run after this operation is done
   ratmr_t startTime;                   //!<        Absolute or relative start time (depending on the value of <code>startTrigger</code>)
   struct {
      uint8_t triggerType:4;            //!<        The type of trigger
      uint8_t bEnaCmd:1;                //!< \brief 0: No alternative trigger command<br>
                                        //!<        1: CMD_TRIGGER can be used as an alternative trigger
      uint8_t triggerNo:2;              //!<        The trigger number of the CMD_TRIGGER command that triggers this action
      uint8_t pastTrig:1;               //!< \brief 0: A trigger in the past is never triggered, or for start of commands, give an error<br>
                                        //!<        1: A trigger in the past is triggered as soon as possible
   } startTrigger;                      //!<        Identification of the trigger that starts the operation
   struct {
      uint8_t rule:4;                   //!<        Condition for running next command: Rule for how to proceed
      uint8_t nSkip:4;                  //!<        Number of skips + 1 if the rule involves skipping. 0: same, 1: next, 2: skip next, ...
   } condition;
   uint8_t channel;                     //!< \brief Channel to use<br>
                                        //!<        0--39: BLE advertising/data channel index<br>
                                        //!<        60--207: Custom frequency; (2300 + <code>channel</code>) MHz<br>
                                        //!<        255: Use existing frequency<br>
                                        //!<        Others: <i>Reserved</i>
   struct {
      uint8_t init:7;                   //!< \brief If <code>bOverride</code> = 1 or custom frequency is used:<br>
                                        //!<        0: Do not use whitening<br>
                                        //!<        Other value: Initialization for 7-bit LFSR whitener
      uint8_t bOverride:1;              //!< \brief 0: Use default whitening for BLE advertising/data channels<br>
                                        //!<        1: Override whitening initialization with value of init
   } whitening;
   struct {
      uint8_t mainMode:2;               //!< \brief PHY to use:<br>
                                        //!<        0: 1 Mbps<br>
                                        //!<        1: 2 Mbps<br>
                                        //!<        2: Coded<br>
                                        //!<        3: <i>Reserved</i>
      uint8_t coding:6;                 //!< \brief Coding to use for TX if coded PHY is selected.
                                        //!<        See the Technical Reference Manual for details.
   } phyMode;
   uint8_t rangeDelay;                  //!<        Number of RAT ticks to add to the listening time after T_IFS
   uint16_t txPower;                    //!< \brief Transmit power to use (overrides the one given in radio setup).
                                        //!<        0x0000: Use default TX power.
   rfc_bleAdvPar_t *pParams;            //!<        Pointer to command specific parameter structure
   rfc_bleAdvOutput_t *pOutput;         //!<        Pointer to command specific output structure
} __RFC_STRUCT_ATTR;

//! @}

//! \addtogroup bleMasterSlavePar
//! @{
struct __RFC_STRUCT rfc_bleMasterSlavePar_s {
   dataQueue_t* pRxQ;                   //!<        Pointer to receive queue
   dataQueue_t* pTxQ;                   //!<        Pointer to transmit queue
   struct {
      uint8_t bAutoFlushIgnored:1;      //!<        If 1, automatically remove ignored packets from Rx queue
      uint8_t bAutoFlushCrcErr:1;       //!<        If 1, automatically remove packets with CRC error from Rx queue
      uint8_t bAutoFlushEmpty:1;        //!<        If 1, automatically remove empty packets from Rx queue
      uint8_t bIncludeLenByte:1;        //!<        If 1, include the received length byte in the stored packet; otherwise discard it
      uint8_t bIncludeCrc:1;            //!<        If 1, include the received CRC field in the stored packet; otherwise discard it
      uint8_t bAppendRssi:1;            //!<        If 1, append an RSSI byte to the packet in the Rx queue
      uint8_t bAppendStatus:1;          //!<        If 1, append a status word to the packet in the Rx queue
      uint8_t bAppendTimestamp:1;       //!<        If 1, append a timestamp to the packet in the Rx queue
   } rxConfig;                          //!<        Configuration bits for the receive queue entries
   struct {
      uint8_t lastRxSn:1;               //!<        The SN bit of the header of the last packet received with CRC OK
      uint8_t lastTxSn:1;               //!<        The SN bit of the header of the last transmitted packet
      uint8_t nextTxSn:1;               //!<        The SN bit of the header of the next packet to transmit
      uint8_t bFirstPkt:1;              //!<        For slave: 0 if a packet has been transmitted on the connection, 1 otherwise
      uint8_t bAutoEmpty:1;             //!<        1 if the last transmitted packet was an auto-empty packet
      uint8_t bLlCtrlTx:1;              //!<        1 if the last transmitted packet was an LL control packet (LLID = 11)
      uint8_t bLlCtrlAckRx:1;           //!<        1 if the last received packet was the ACK of an LL control packet
      uint8_t bLlCtrlAckPending:1;      //!<        1 if the last successfully received packet was an LL control packet which has not yet been ACK'ed
   } seqStat;                           //!<        Sequence number status
   uint8_t maxNack;                     //!<        Maximum number of NACKs received before operation ends. 0: No limit
   uint8_t maxPkt;                      //!<        Maximum number of packets transmitted in the operation before it ends. 0: No limit
   uint32_t accessAddress;              //!<        Access address used on the connection
   uint8_t crcInit0;                    //!<        CRC initialization value used on the connection -- least significant byte
   uint8_t crcInit1;                    //!<        CRC initialization value used on the connection -- middle byte
   uint8_t crcInit2;                    //!<        CRC initialization value used on the connection -- most significant byte
} __RFC_STRUCT_ATTR;

//! @}

//! \addtogroup bleSlavePar
//! @{
//! Parameter structure for legacy slave (CMD_BLE_SLAVE)

struct __RFC_STRUCT rfc_bleSlavePar_s {
   dataQueue_t* pRxQ;                   //!<        Pointer to receive queue
   dataQueue_t* pTxQ;                   //!<        Pointer to transmit queue
   struct {
      uint8_t bAutoFlushIgnored:1;      //!<        If 1, automatically remove ignored packets from Rx queue
      uint8_t bAutoFlushCrcErr:1;       //!<        If 1, automatically remove packets with CRC error from Rx queue
      uint8_t bAutoFlushEmpty:1;        //!<        If 1, automatically remove empty packets from Rx queue
      uint8_t bIncludeLenByte:1;        //!<        If 1, include the received length byte in the stored packet; otherwise discard it
      uint8_t bIncludeCrc:1;            //!<        If 1, include the received CRC field in the stored packet; otherwise discard it
      uint8_t bAppendRssi:1;            //!<        If 1, append an RSSI byte to the packet in the Rx queue
      uint8_t bAppendStatus:1;          //!<        If 1, append a status word to the packet in the Rx queue
      uint8_t bAppendTimestamp:1;       //!<        If 1, append a timestamp to the packet in the Rx queue
   } rxConfig;                          //!<        Configuration bits for the receive queue entries
   struct {
      uint8_t lastRxSn:1;               //!<        The SN bit of the header of the last packet received with CRC OK
      uint8_t lastTxSn:1;               //!<        The SN bit of the header of the last transmitted packet
      uint8_t nextTxSn:1;               //!<        The SN bit of the header of the next packet to transmit
      uint8_t bFirstPkt:1;              //!<        For slave: 0 if a packet has been transmitted on the connection, 1 otherwise
      uint8_t bAutoEmpty:1;             //!<        1 if the last transmitted packet was an auto-empty packet
      uint8_t bLlCtrlTx:1;              //!<        1 if the last transmitted packet was an LL control packet (LLID = 11)
      uint8_t bLlCtrlAckRx:1;           //!<        1 if the last received packet was the ACK of an LL control packet
      uint8_t bLlCtrlAckPending:1;      //!<        1 if the last successfully received packet was an LL control packet which has not yet been ACK'ed
   } seqStat;                           //!<        Sequence number status
   uint8_t maxNack;                     //!<        Maximum number of NACKs received before operation ends. 0: No limit
   uint8_t maxPkt;                      //!<        Maximum number of packets transmitted in the operation before it ends. 0: No limit
   uint32_t accessAddress;              //!<        Access address used on the connection
   uint8_t crcInit0;                    //!<        CRC initialization value used on the connection -- least significant byte
   uint8_t crcInit1;                    //!<        CRC initialization value used on the connection -- middle byte
   uint8_t crcInit2;                    //!<        CRC initialization value used on the connection -- most significant byte
   struct {
      uint8_t triggerType:4;            //!<        The type of trigger
      uint8_t bEnaCmd:1;                //!< \brief 0: No alternative trigger command<br>
                                        //!<        1: CMD_TRIGGER can be used as an alternative trigger
      uint8_t triggerNo:2;              //!<        The trigger number of the CMD_TRIGGER command that triggers this action
      uint8_t pastTrig:1;               //!< \brief 0: A trigger in the past is never triggered, or for start of commands, give an error<br>
                                        //!<        1: A trigger in the past is triggered as soon as possible
   } timeoutTrigger;                    //!<        Trigger that defines timeout of the first receive operation
   ratmr_t timeoutTime;                 //!< \brief Time used together with <code>timeoutTrigger</code> that defines timeout of the first
                                        //!<        receive operation
   uint16_t __dummy0;
   uint8_t __dummy1;
   struct {
      uint8_t triggerType:4;            //!<        The type of trigger
      uint8_t bEnaCmd:1;                //!< \brief 0: No alternative trigger command<br>
                                        //!<        1: CMD_TRIGGER can be used as an alternative trigger
      uint8_t triggerNo:2;              //!<        The trigger number of the CMD_TRIGGER command that triggers this action
      uint8_t pastTrig:1;               //!< \brief 0: A trigger in the past is never triggered, or for start of commands, give an error<br>
                                        //!<        1: A trigger in the past is triggered as soon as possible
   } endTrigger;                        //!<        Trigger that causes the device to end the connection event as soon as allowed
   ratmr_t endTime;                     //!< \brief Time used together with <code>endTrigger</code> that causes the device to end the
                                        //!<        connection event as soon as allowed
} __RFC_STRUCT_ATTR;

//! @}

//! \addtogroup bleMasterPar
//! @{
//! Parameter structure for legacy master (CMD_BLE_MASTER)

struct __RFC_STRUCT rfc_bleMasterPar_s {
   dataQueue_t* pRxQ;                   //!<        Pointer to receive queue
   dataQueue_t* pTxQ;                   //!<        Pointer to transmit queue
   struct {
      uint8_t bAutoFlushIgnored:1;      //!<        If 1, automatically remove ignored packets from Rx queue
      uint8_t bAutoFlushCrcErr:1;       //!<        If 1, automatically remove packets with CRC error from Rx queue
      uint8_t bAutoFlushEmpty:1;        //!<        If 1, automatically remove empty packets from Rx queue
      uint8_t bIncludeLenByte:1;        //!<        If 1, include the received length byte in the stored packet; otherwise discard it
      uint8_t bIncludeCrc:1;            //!<        If 1, include the received CRC field in the stored packet; otherwise discard it
      uint8_t bAppendRssi:1;            //!<        If 1, append an RSSI byte to the packet in the Rx queue
      uint8_t bAppendStatus:1;          //!<        If 1, append a status word to the packet in the Rx queue
      uint8_t bAppendTimestamp:1;       //!<        If 1, append a timestamp to the packet in the Rx queue
   } rxConfig;                          //!<        Configuration bits for the receive queue entries
   struct {
      uint8_t lastRxSn:1;               //!<        The SN bit of the header of the last packet received with CRC OK
      uint8_t lastTxSn:1;               //!<        The SN bit of the header of the last transmitted packet
      uint8_t nextTxSn:1;               //!<        The SN bit of the header of the next packet to transmit
      uint8_t bFirstPkt:1;              //!<        For slave: 0 if a packet has been transmitted on the connection, 1 otherwise
      uint8_t bAutoEmpty:1;             //!<        1 if the last transmitted packet was an auto-empty packet
      uint8_t bLlCtrlTx:1;              //!<        1 if the last transmitted packet was an LL control packet (LLID = 11)
      uint8_t bLlCtrlAckRx:1;           //!<        1 if the last received packet was the ACK of an LL control packet
      uint8_t bLlCtrlAckPending:1;      //!<        1 if the last successfully received packet was an LL control packet which has not yet been ACK'ed
   } seqStat;                           //!<        Sequence number status
   uint8_t maxNack;                     //!<        Maximum number of NACKs received before operation ends. 0: No limit
   uint8_t maxPkt;                      //!<        Maximum number of packets transmitted in the operation before it ends. 0: No limit
   uint32_t accessAddress;              //!<        Access address used on the connection
   uint8_t crcInit0;                    //!<        CRC initialization value used on the connection -- least significant byte
   uint8_t crcInit1;                    //!<        CRC initialization value used on the connection -- middle byte
   uint8_t crcInit2;                    //!<        CRC initialization value used on the connection -- most significant byte
   struct {
      uint8_t triggerType:4;            //!<        The type of trigger
      uint8_t bEnaCmd:1;                //!< \brief 0: No alternative trigger command<br>
                                        //!<        1: CMD_TRIGGER can be used as an alternative trigger
      uint8_t triggerNo:2;              //!<        The trigger number of the CMD_TRIGGER command that triggers this action
      uint8_t pastTrig:1;               //!< \brief 0: A trigger in the past is never triggered, or for start of commands, give an error<br>
                                        //!<        1: A trigger in the past is triggered as soon as possible
   } endTrigger;                        //!<        Trigger that causes the device to end the connection event as soon as allowed
   ratmr_t endTime;                     //!< \brief Time used together with <code>endTrigger</code> that causes the device to end the
                                        //!<        connection event as soon as allowed
} __RFC_STRUCT_ATTR;

//! @}

//! \addtogroup bleAdvPar
//! @{
//! Parameter structure for legacy advertiser (CMD_BLE_ADV* and CMD_BLE5_ADV*)

struct __RFC_STRUCT rfc_bleAdvPar_s {
   dataQueue_t* pRxQ;                   //!<        Pointer to receive queue
   struct {
      uint8_t bAutoFlushIgnored:1;      //!<        If 1, automatically remove ignored packets from Rx queue
      uint8_t bAutoFlushCrcErr:1;       //!<        If 1, automatically remove packets with CRC error from Rx queue
      uint8_t bAutoFlushEmpty:1;        //!<        If 1, automatically remove empty packets from Rx queue
      uint8_t bIncludeLenByte:1;        //!<        If 1, include the received length byte in the stored packet; otherwise discard it
      uint8_t bIncludeCrc:1;            //!<        If 1, include the received CRC field in the stored packet; otherwise discard it
      uint8_t bAppendRssi:1;            //!<        If 1, append an RSSI byte to the packet in the Rx queue
      uint8_t bAppendStatus:1;          //!<        If 1, append a status word to the packet in the Rx queue
      uint8_t bAppendTimestamp:1;       //!<        If 1, append a timestamp to the packet in the Rx queue
   } rxConfig;                          //!<        Configuration bits for the receive queue entries
   struct {
      uint8_t advFilterPolicy:2;        //!< \brief Advertiser filter policy<br>
                                        //!<        0: Process scan and connect requests from all devices<br>
                                        //!<        1: Process connect requests from all devices and only scan requests from
                                        //!<        devices that are in the white list<br>
                                        //!<        2: Process scan requests from all devices and only connect requests from
                                        //!<        devices that are in the white list<br>
                                        //!<        3: Process scan and connect requests only from devices in the white list
      uint8_t deviceAddrType:1;         //!<        The type of the device address -- public (0) or random (1)
      uint8_t peerAddrType:1;           //!<        Directed advertiser: The type of the peer address -- public (0) or random (1)
      uint8_t bStrictLenFilter:1;       //!< \brief 0: Accept any packet with a valid advertising packet length<br>
                                        //!<        1: Discard messages with illegal length for the given packet type
      uint8_t chSel:1;                  //!< \brief 0: Do not report support of Channel Selection Algorithm #2<br>
                                        //!<        1: Report support of Channel Selection Algorithm #2 (patch required)
      uint8_t privIgnMode:1;            //!< \brief 0: Filter on bPrivIgn only when white list is used (if patch is used)
                                        //!<        1: Filter on bPrivIgn always (patch required)
      uint8_t rpaMode:1;                //!< \brief Resolvable private address mode<br>
                                        //!<        0: Normal operation<br>
                                        //!<        1: Use white list for a received RPA regardless of filter policy
   } advConfig;
   uint8_t advLen;                      //!<        Size of advertiser data
   uint8_t scanRspLen;                  //!<        Size of scan response data
   uint8_t* pAdvData;                   //!<        Pointer to buffer containing ADV*_IND data
   uint8_t* pScanRspData;               //!<        Pointer to buffer containing SCAN_RSP data
   uint16_t* pDeviceAddress;            //!< \brief Pointer (with least significant bit set to 0) to device address used for this device.
                                        //!<        If least significant bit is 1, the address type given by
                                        //!<        <code>advConfig.deviceAddrType</code> is inverted.
   rfc_bleWhiteListEntry_t *pWhiteList; //!< \brief Pointer (with least significant bit set to 0)  to white list or peer address (directed
                                        //!<        advertiser). If least significant bit is 1, the address type given by
                                        //!<        <code>advConfig.peerAddrType</code> is inverted.
   uint16_t __dummy0;
   uint8_t __dummy1;
   struct {
      uint8_t triggerType:4;            //!<        The type of trigger
      uint8_t bEnaCmd:1;                //!< \brief 0: No alternative trigger command<br>
                                        //!<        1: CMD_TRIGGER can be used as an alternative trigger
      uint8_t triggerNo:2;              //!<        The trigger number of the CMD_TRIGGER command that triggers this action
      uint8_t pastTrig:1;               //!< \brief 0: A trigger in the past is never triggered, or for start of commands, give an error<br>
                                        //!<        1: A trigger in the past is triggered as soon as possible
   } endTrigger;                        //!<        Trigger that causes the device to end the advertiser event as soon as allowed
   ratmr_t endTime;                     //!< \brief Time used together with <code>endTrigger</code> that causes the device to end the
                                        //!<        advertiser event as soon as allowed
} __RFC_STRUCT_ATTR;

//! @}

//! \addtogroup bleScannerPar
//! @{
//! Parameter structure for legacy scanner (CMD_BLE_SCANNER)
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
