tayspen72/BluetoothBlinker/BluetoothBlinker-MCU-c/cc26x0r2/driverlib/rfc.c

/******************************************************************************
*  Filename:       rfc.c
*  Revised:        2018-08-08 11:04:37 +0200 (Wed, 08 Aug 2018)
*  Revision:       52334
*
*  Description:    Driver for the RF Core.
*
*  Copyright (c) 2015 - 2017, Texas Instruments Incorporated
*  All rights reserved.
*
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
*  3) Neither the name of the ORGANIZATION nor the names of its contributors may
*     be used to endorse or promote products derived from this software without
*     specific prior written permission.
*
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
******************************************************************************/

#include "rfc.h"
#include "rf_mailbox.h"
#include <string.h>

//*****************************************************************************
//
// Handle support for DriverLib in ROM:
// This section will undo prototype renaming made in the header file
//
//*****************************************************************************
#if !defined(DOXYGEN)
    #undef  RFCCpeIntGetAndClear
    #define RFCCpeIntGetAndClear            NOROM_RFCCpeIntGetAndClear
    #undef  RFCDoorbellSendTo
    #define RFCDoorbellSendTo               NOROM_RFCDoorbellSendTo
    #undef  RFCSynthPowerDown
    #define RFCSynthPowerDown               NOROM_RFCSynthPowerDown
    #undef  RFCCpePatchReset
    #define RFCCpePatchReset                NOROM_RFCCpePatchReset
    #undef  RFCOverrideSearch
    #define RFCOverrideSearch               NOROM_RFCOverrideSearch
    #undef  RFCOverrideUpdate
    #define RFCOverrideUpdate               NOROM_RFCOverrideUpdate
    #undef  RFCHwIntGetAndClear
    #define RFCHwIntGetAndClear             NOROM_RFCHwIntGetAndClear
    #undef  RFCRfTrimRead
    #define RFCRfTrimRead                   NOROM_RFCRfTrimRead
    #undef  RFCRfTrimSet
    #define RFCRfTrimSet                    NOROM_RFCRfTrimSet
    #undef  RFCRTrim
    #define RFCRTrim                        NOROM_RFCRTrim
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
